LucaEstiva/Hobby_8088_PC/CPLD/Immagini/Altera_Quartus_BUS_Controller.png

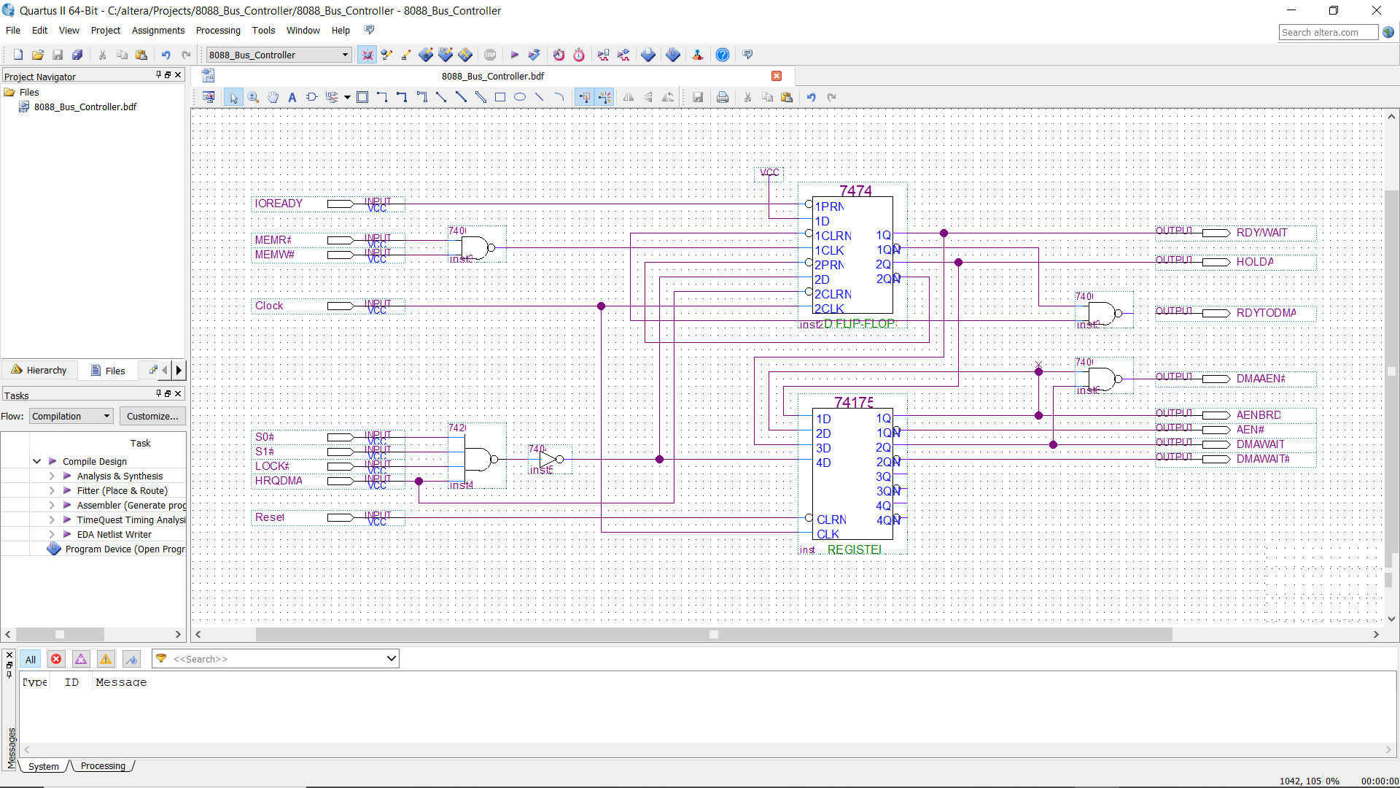
CPLD/Immagini/Altera_Quartus_BUS_Controller.png
