LucaEstiva/Hobby_8088_PC/CPLD/Immagini/USB_Blaster_Descrizione_Segnali.jpg

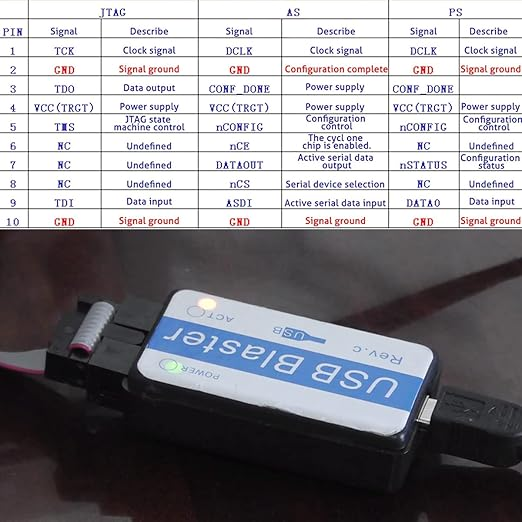
CPLD/Immagini/USB_Blaster_Descrizione_Segnali.jpg
