LucaEstiva/Hobby_8088_PC/Diagrammi/8088_Address_Data_Bus.png

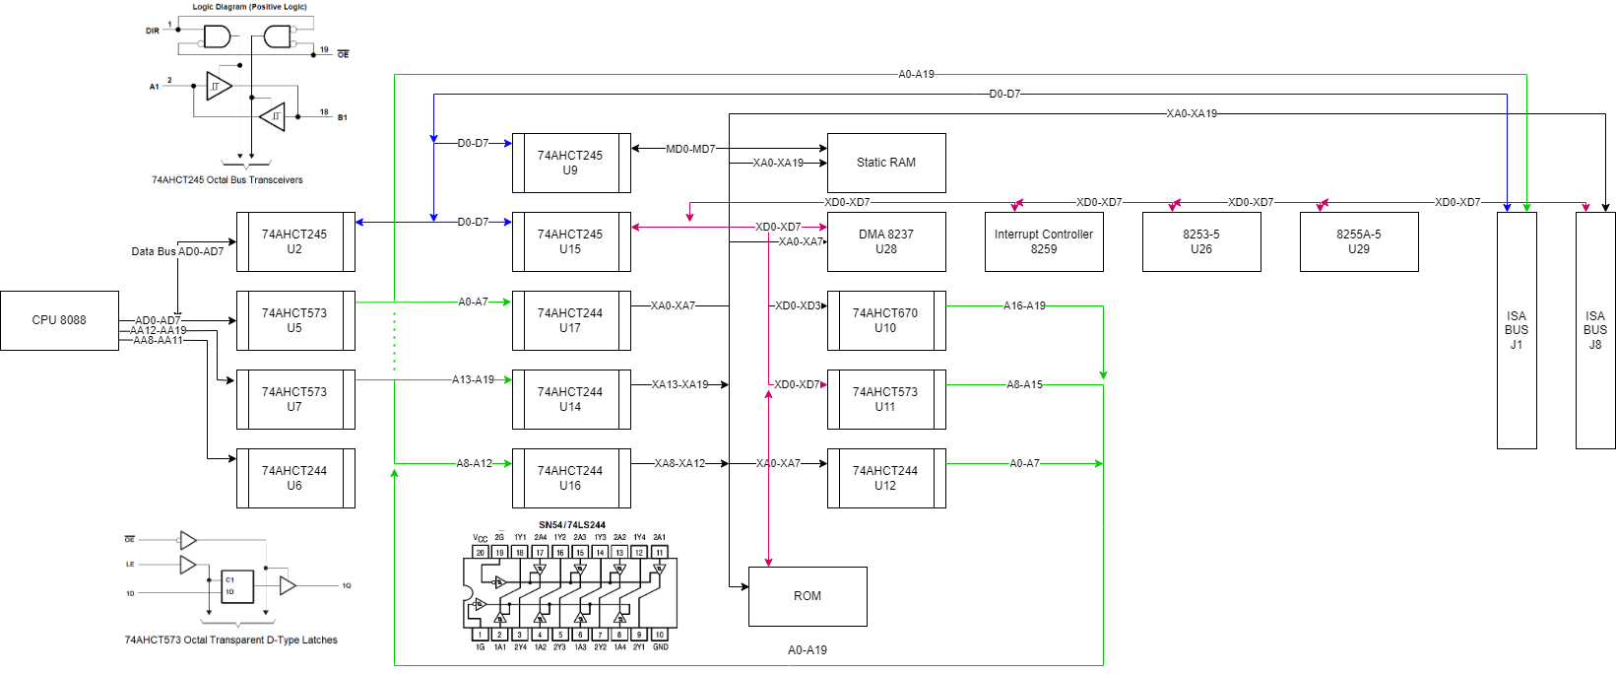
Diagrammi/8088_Address_Data_Bus.png
