LucaEstiva/Hobby_8088_PC/Diagrammi/AT29C010A.png

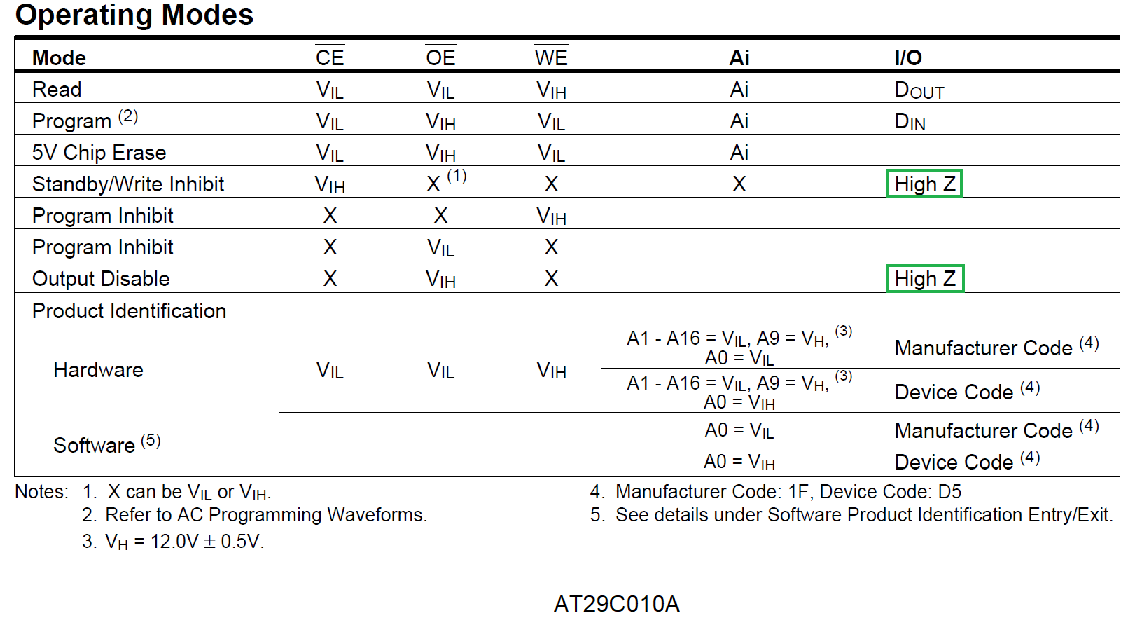
Diagrammi/AT29C010A.png
