LucaEstiva/Hobby_8088_PC/Diagrammi/HM628512C.png

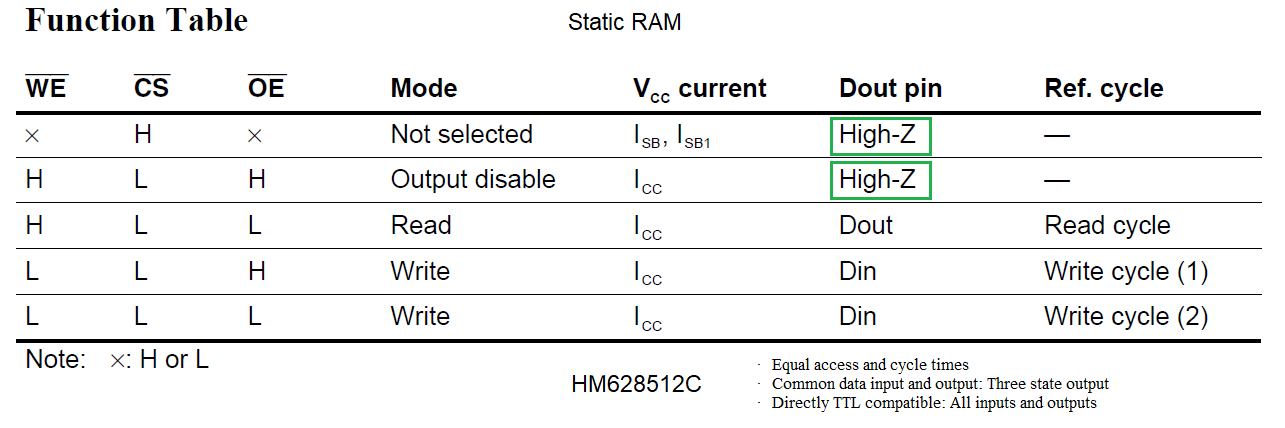
Diagrammi/HM628512C.png
