LucaEstiva/Hobby_8088_PC/FlipFlop/D_Flip-Flop_Async_PRE_CLEAR.png

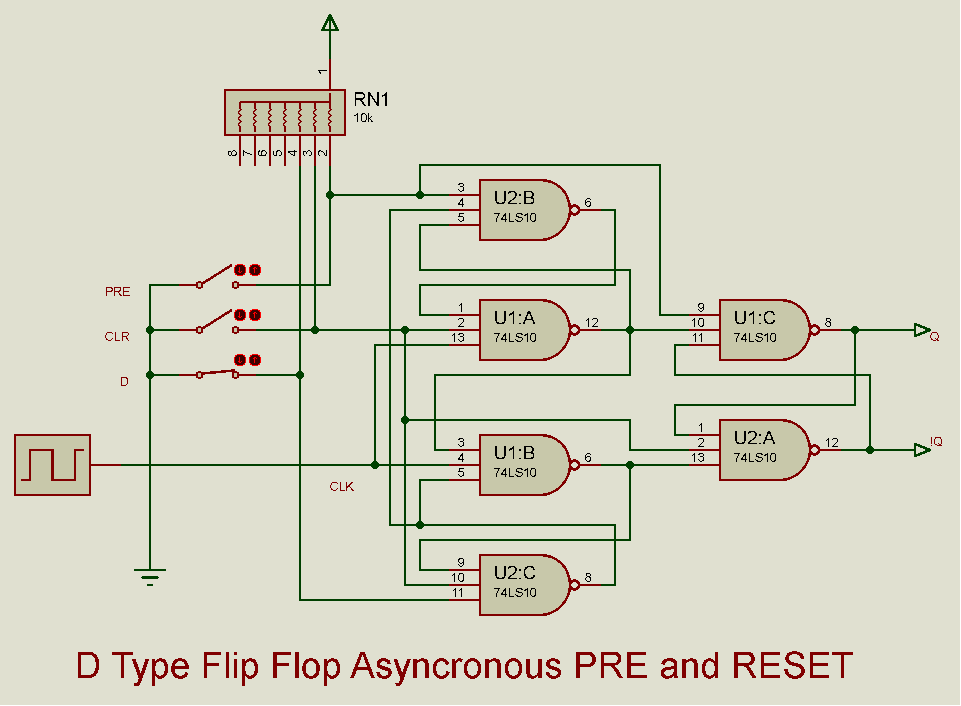
FlipFlop/D_Flip-Flop_Async_PRE_CLEAR.png
