LucaEstiva/Hobby_8088_PC/FlipFlop/D_Pre_Clear.png

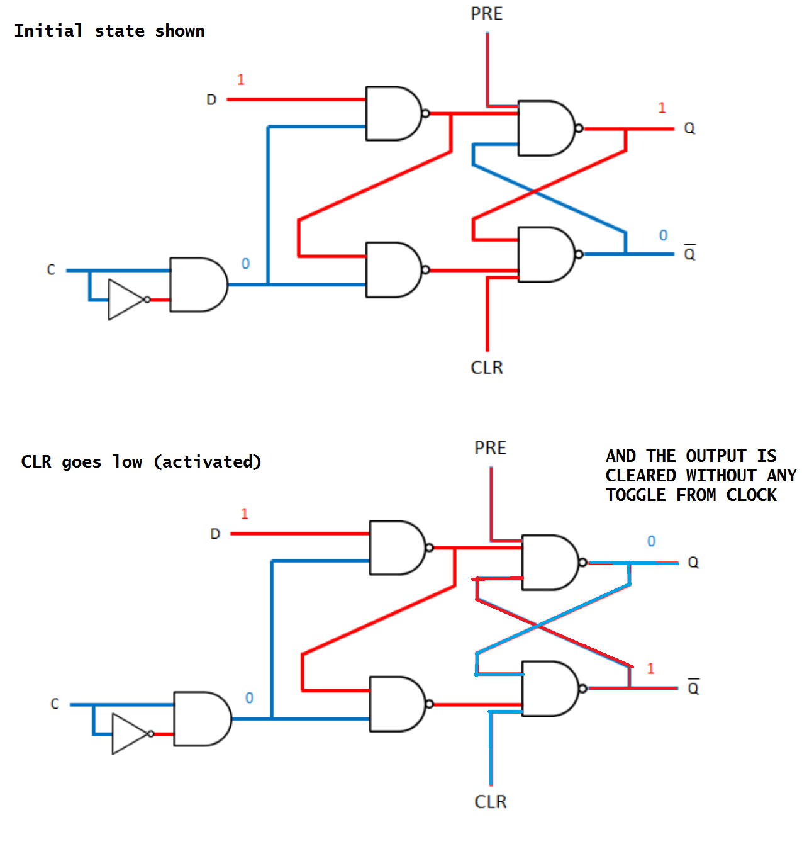
FlipFlop/D_Pre_Clear.png
