LucaEstiva/Hobby_8088_PC/GAL/Async_PRE_CLR.png

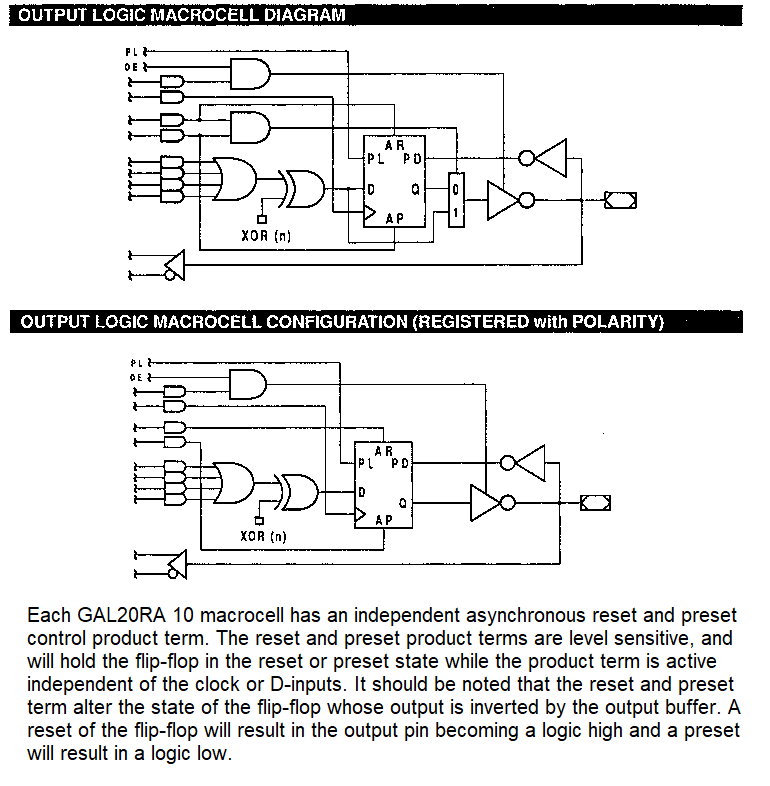
GAL/Async_PRE_CLR.png
