LucaEstiva/Hobby_8088_PC/GAL/Bus_Logic.png

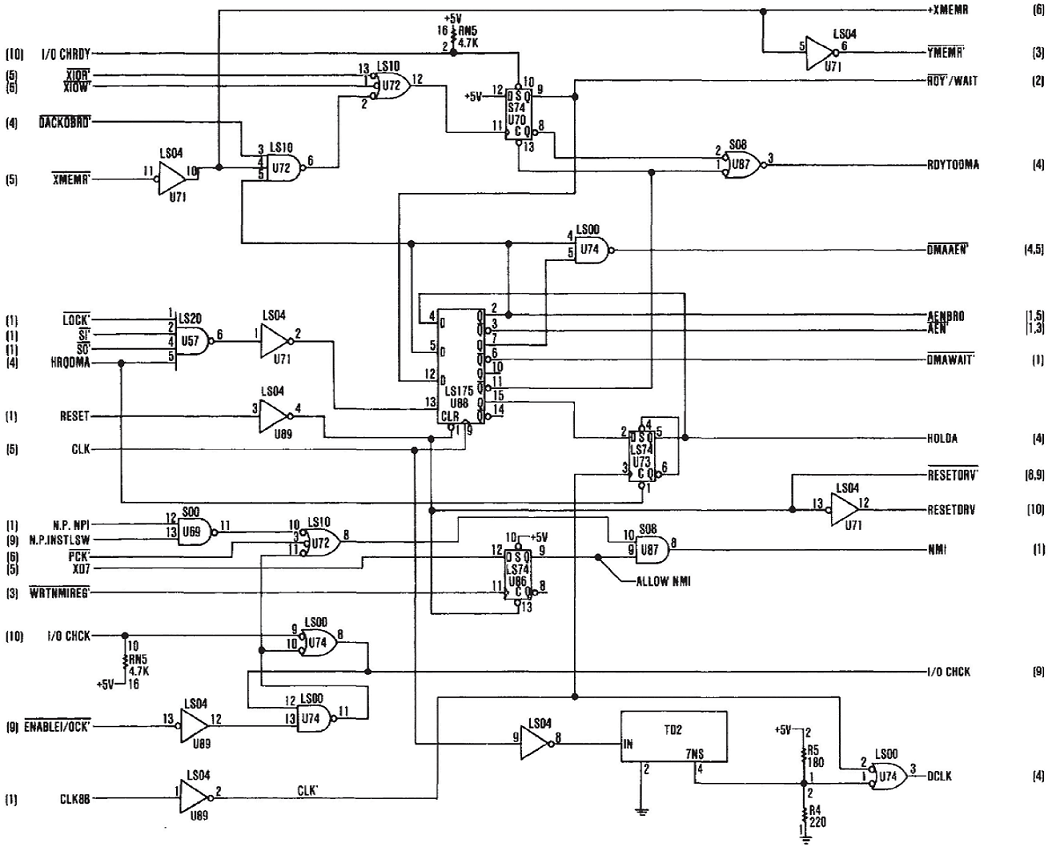
GAL/Bus_Logic.png
