LucaEstiva/Hobby_8088_PC/GAL/Bus_Logic_1.png

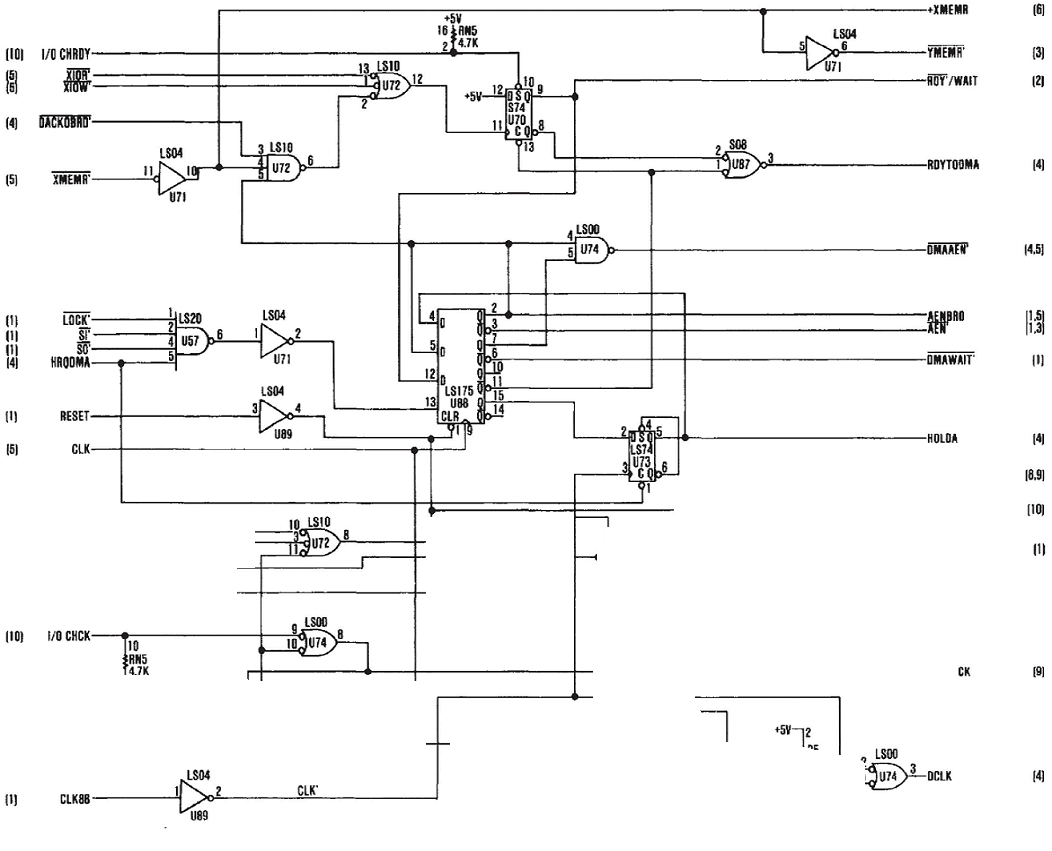
GAL/Bus_Logic_1.png
