LucaEstiva/Hobby_8088_PC/GAL/Bus_Logic_2.png

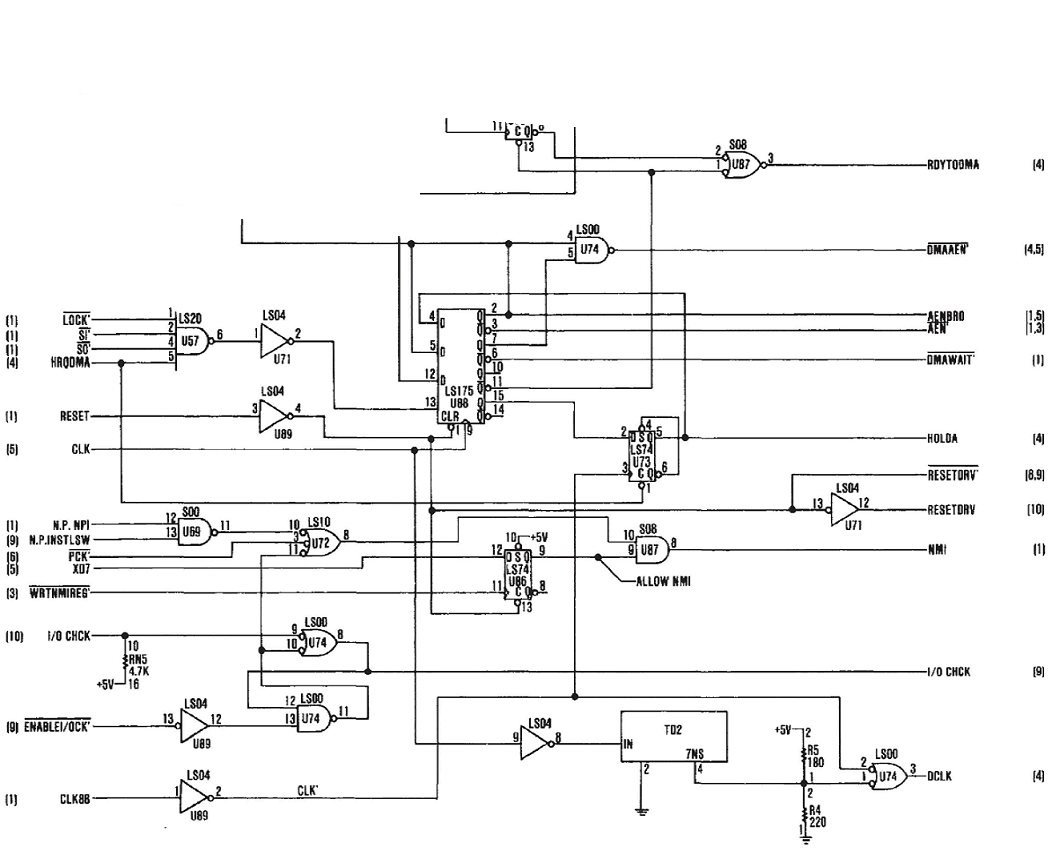
GAL/Bus_Logic_2.png
