LucaEstiva/Hobby_8088_PC/GAL/Bus_Logic_3.png

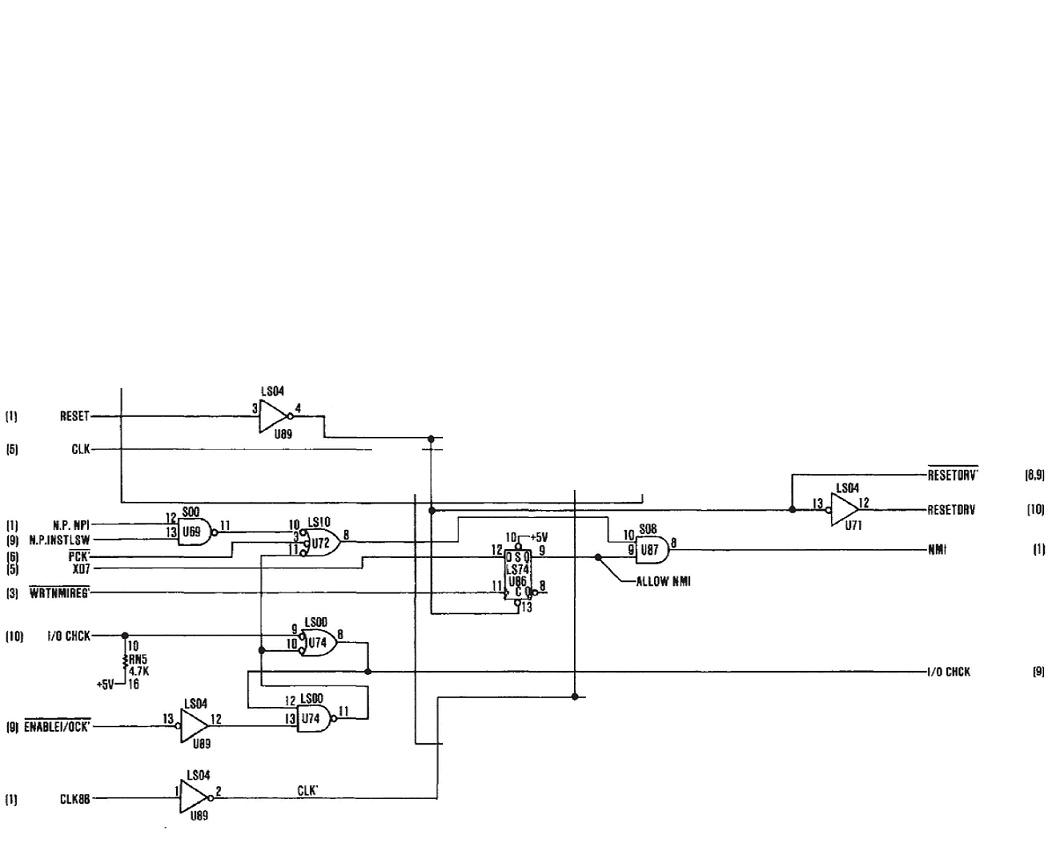
GAL/Bus_Logic_3.png
