LucaEstiva/Hobby_8088_PC/GAL/Bus_Logic_4.png

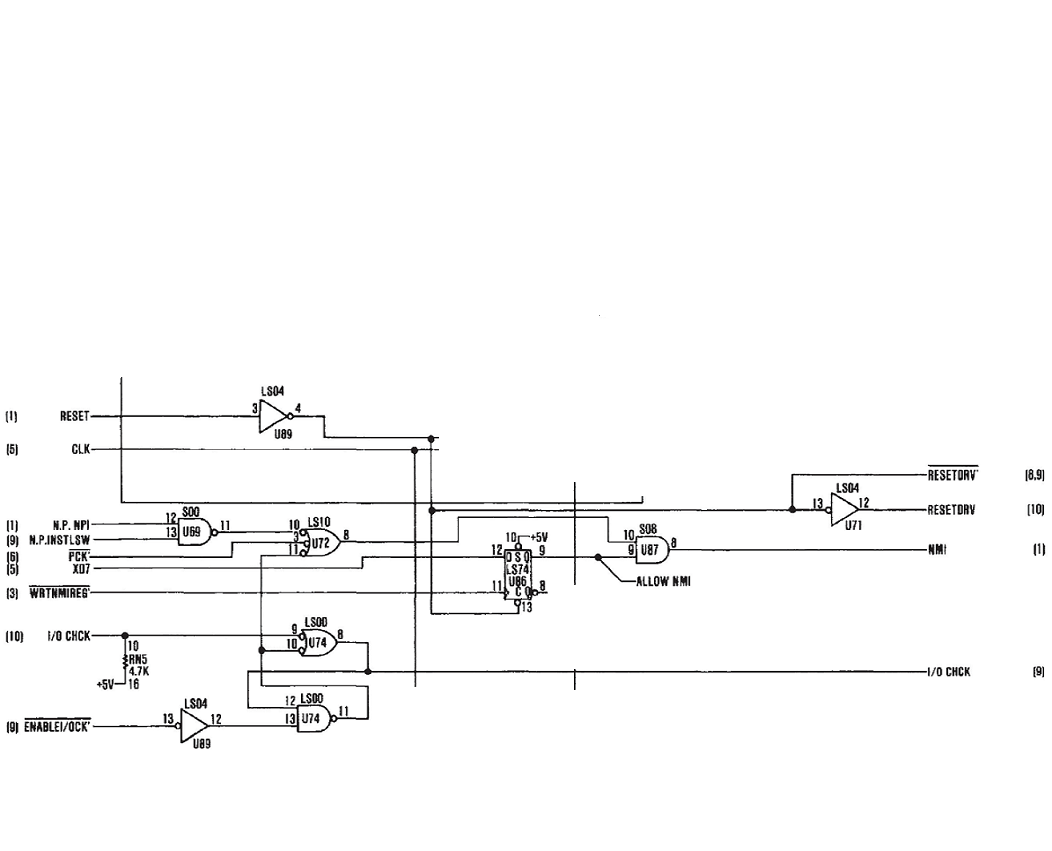
GAL/Bus_Logic_4.png
