LucaEstiva/Hobby_8088_PC/GAL/Bus_Logic_5.png

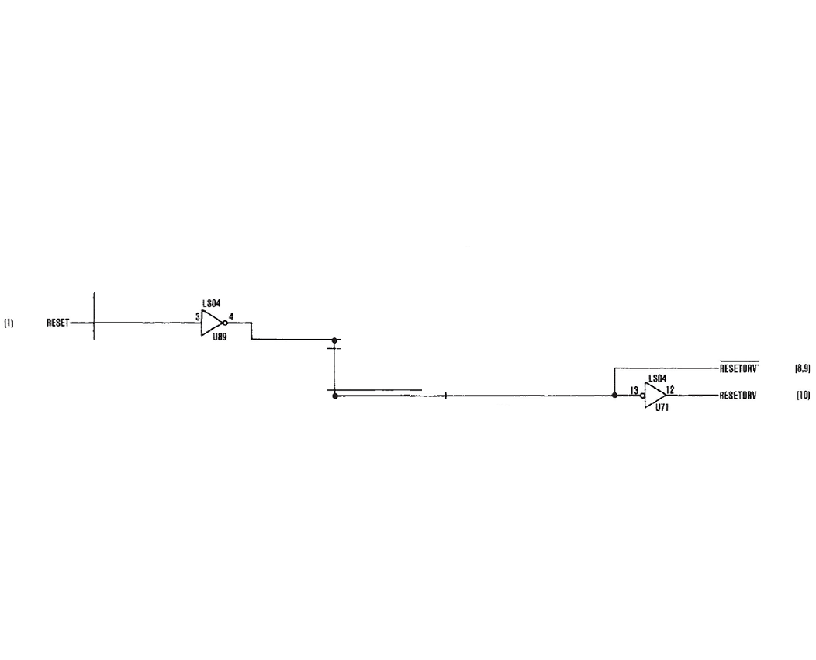
GAL/Bus_Logic_5.png
