LucaEstiva/Hobby_8088_PC/GAL/Bus_Logic_6.png

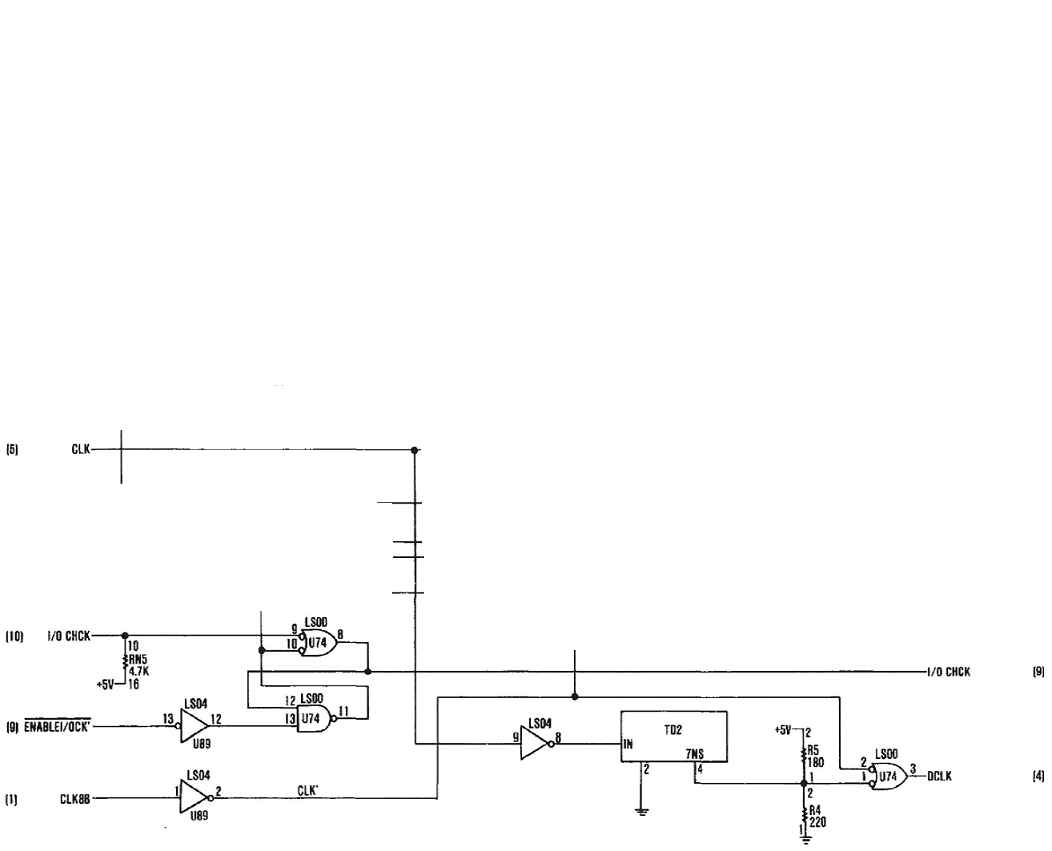
GAL/Bus_Logic_6.png
