LucaEstiva/Hobby_8088_PC/GAL/Bus_Logic_7.png

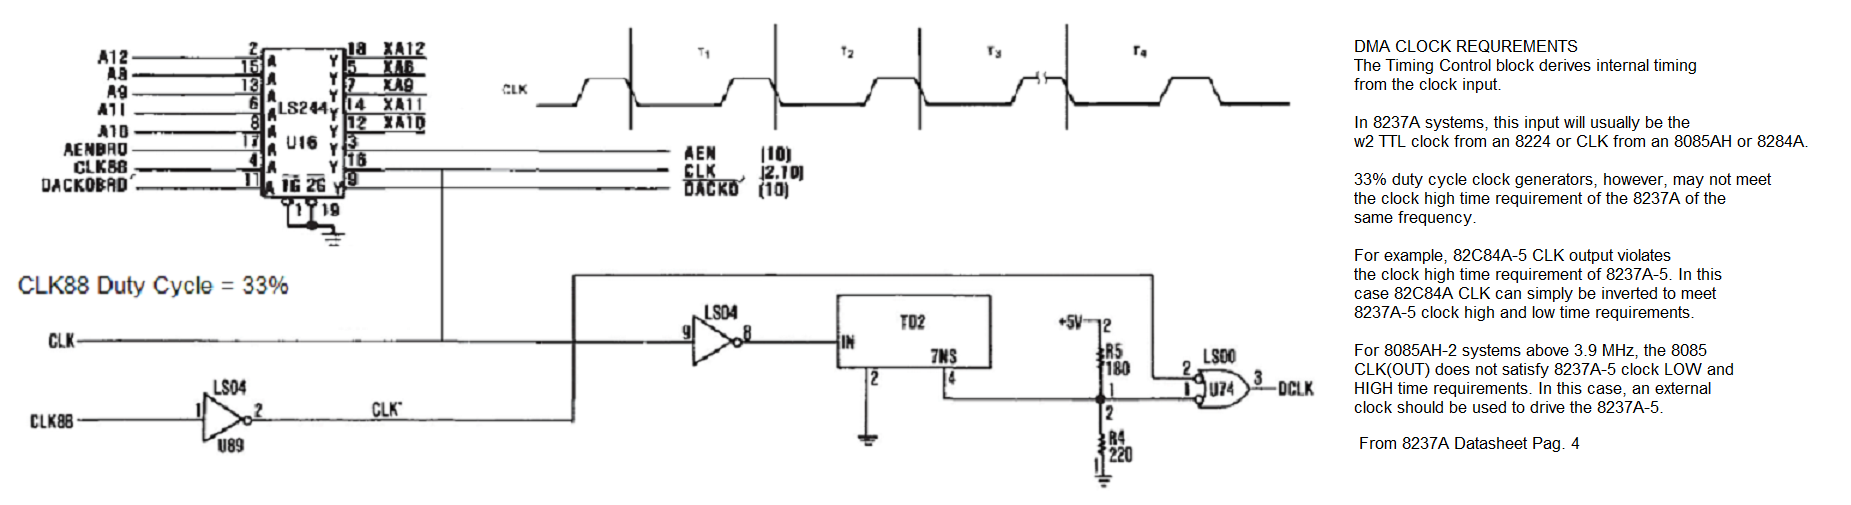
GAL/Bus_Logic_7.png
