LucaEstiva/Hobby_8088_PC/Logica/Bus_Part_1.png

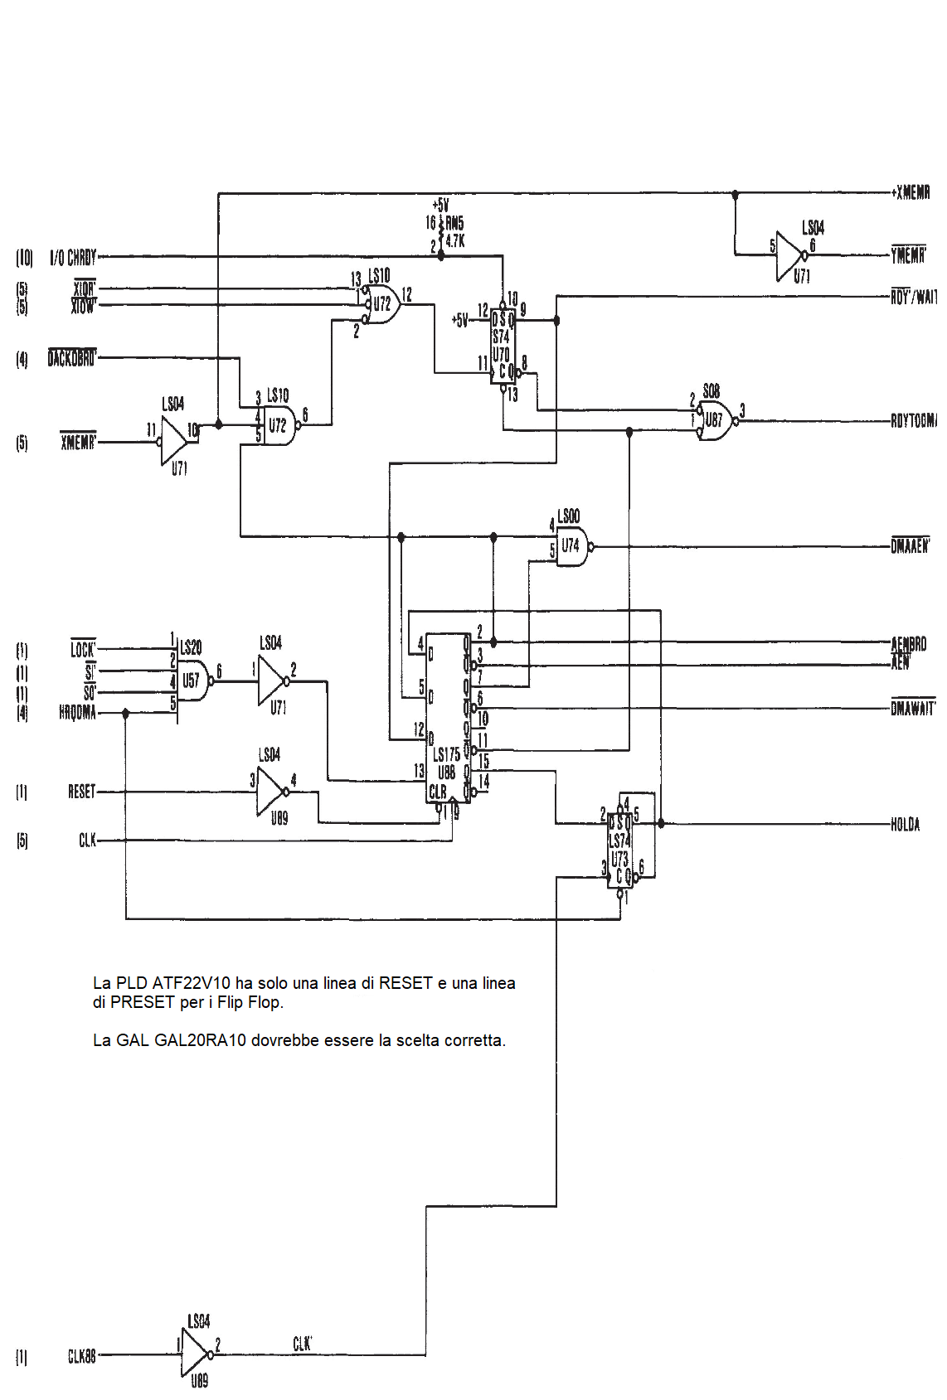
Logica/Bus_Part_1.png
