LucaEstiva/Hobby_8088_PC/Logica/Logic_Gates.png

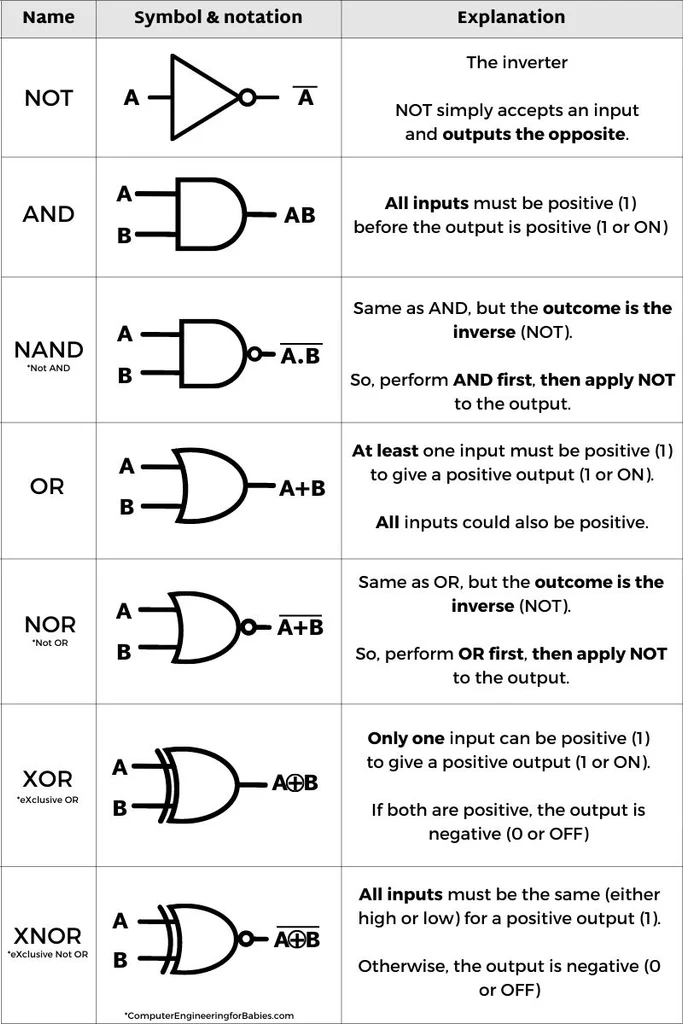
Logica/Logic_Gates.png
