LucaEstiva/Hobby_8088_PC/Simplyfied_Diagram/5150_5160_clock_generation.jpg

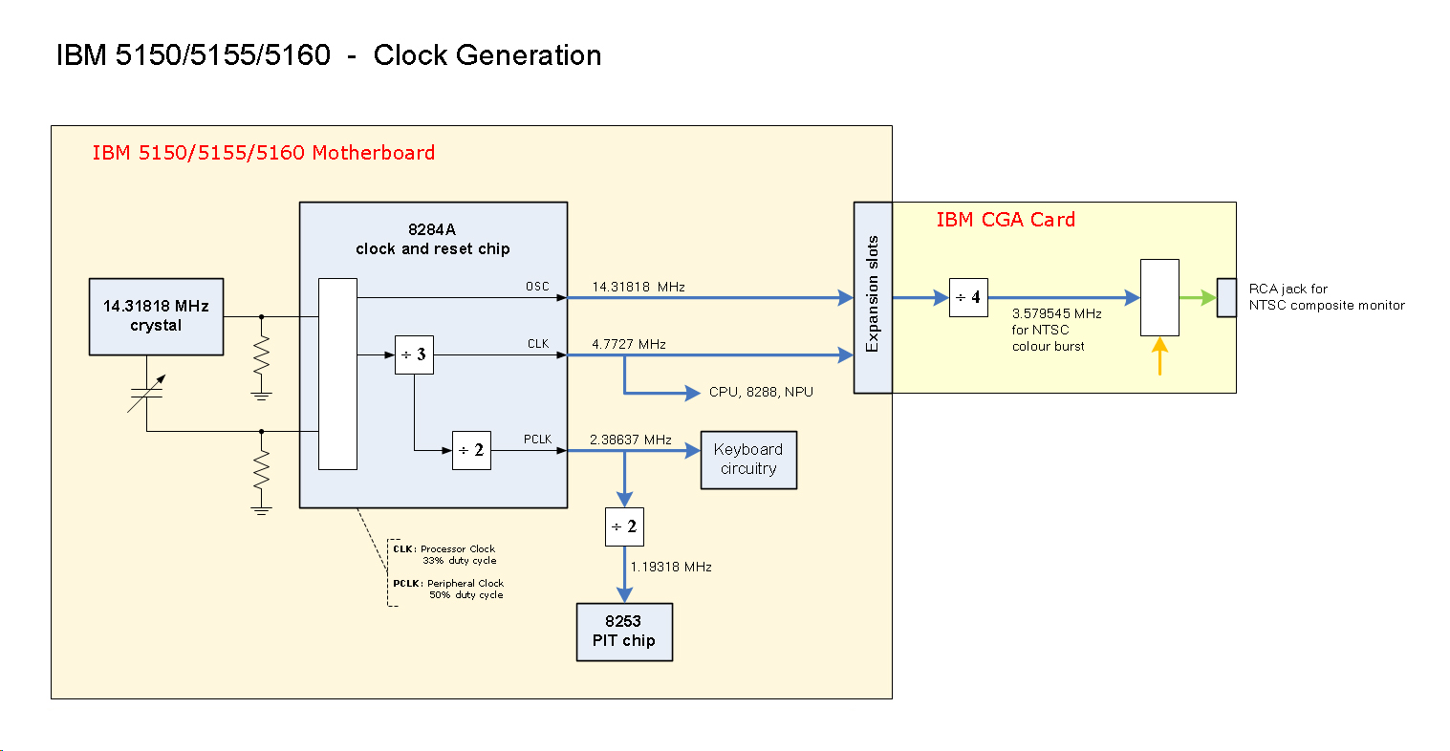
Simplyfied_Diagram/5150_5160_clock_generation.jpg
