LucaEstiva/Hobby_8088_PC/Simplyfied_Diagram/5150_5160_motherboard_ram_layout.jpg

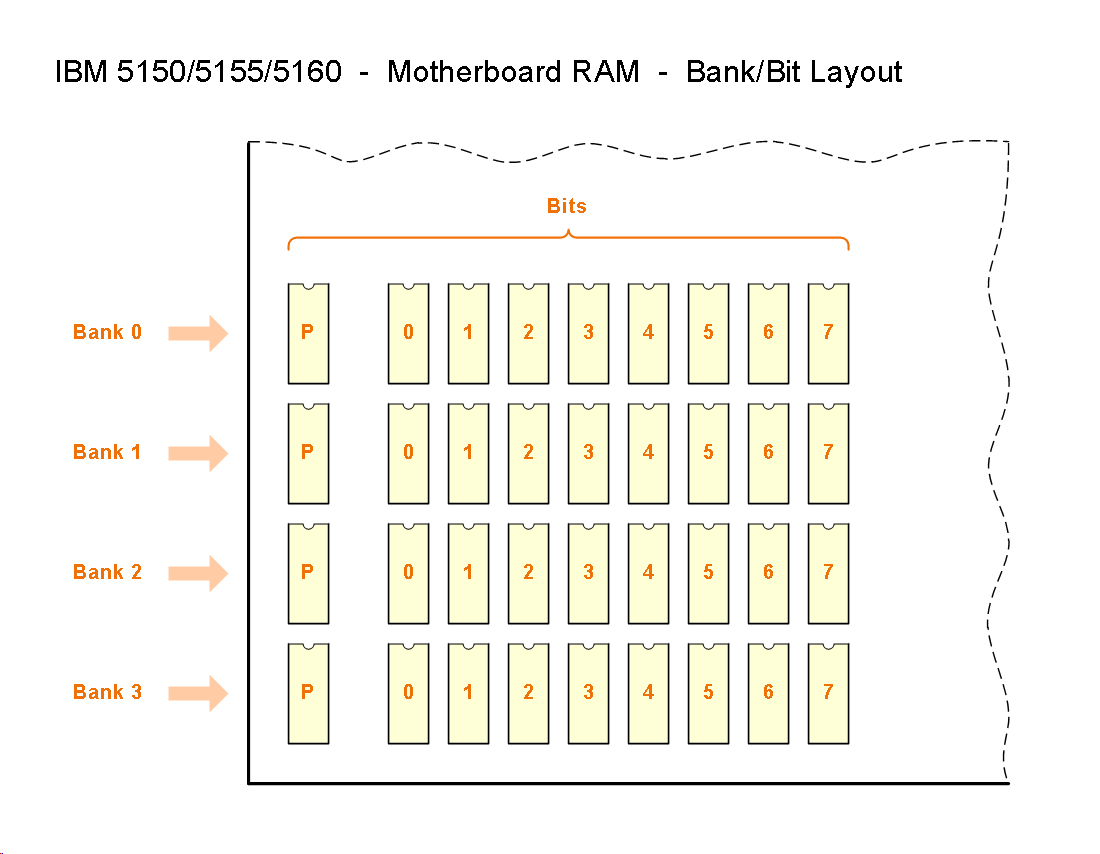
Simplyfied_Diagram/5150_5160_motherboard_ram_layout.jpg
