LucaEstiva/Hobby_8088_PC/Simplyfied_Diagram/5160_address_bus.jpg

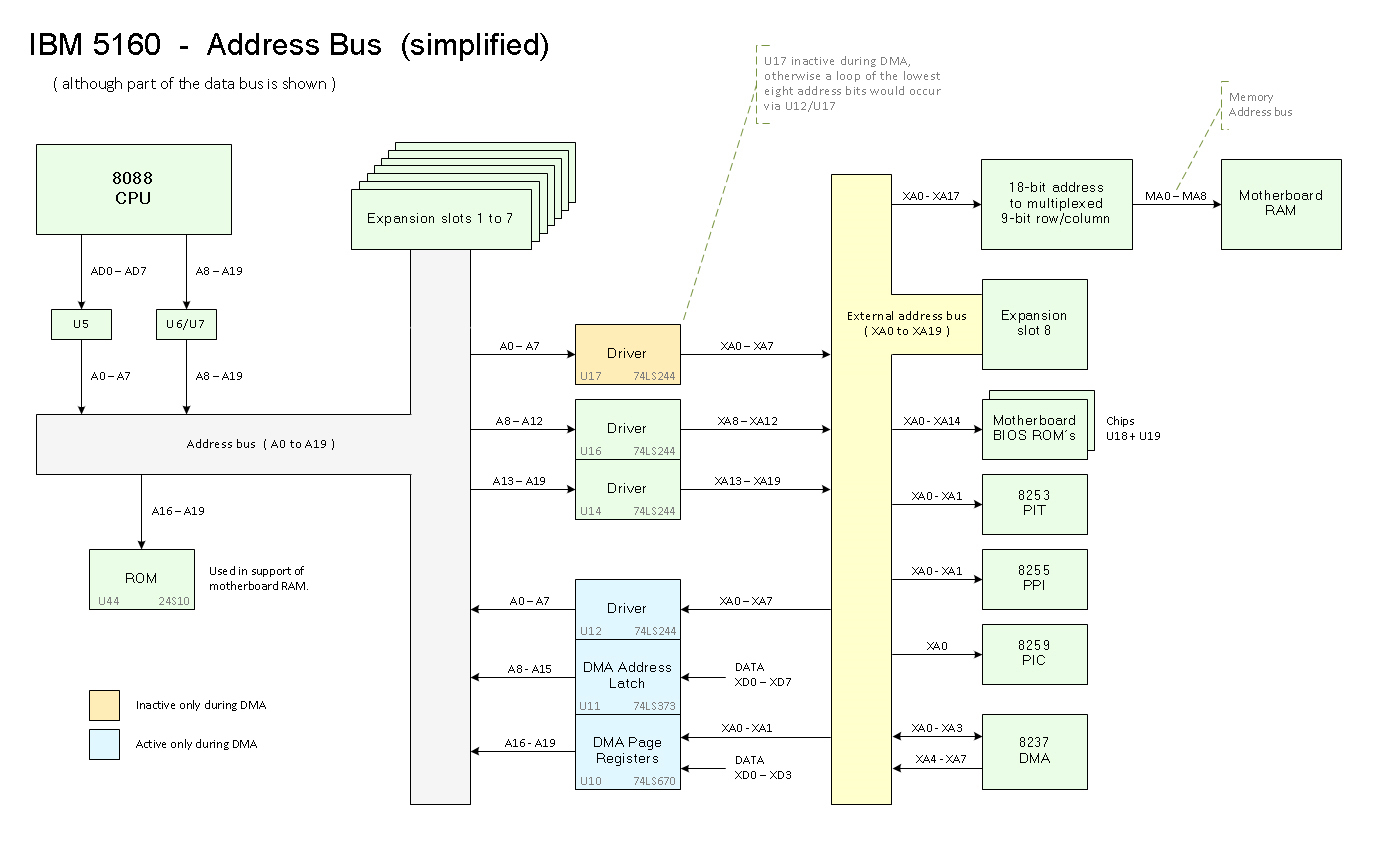
Simplyfied_Diagram/5160_address_bus.jpg
