LucaEstiva/Hobby_8088_PC/Simplyfied_Diagram/5160_data_bus.jpg

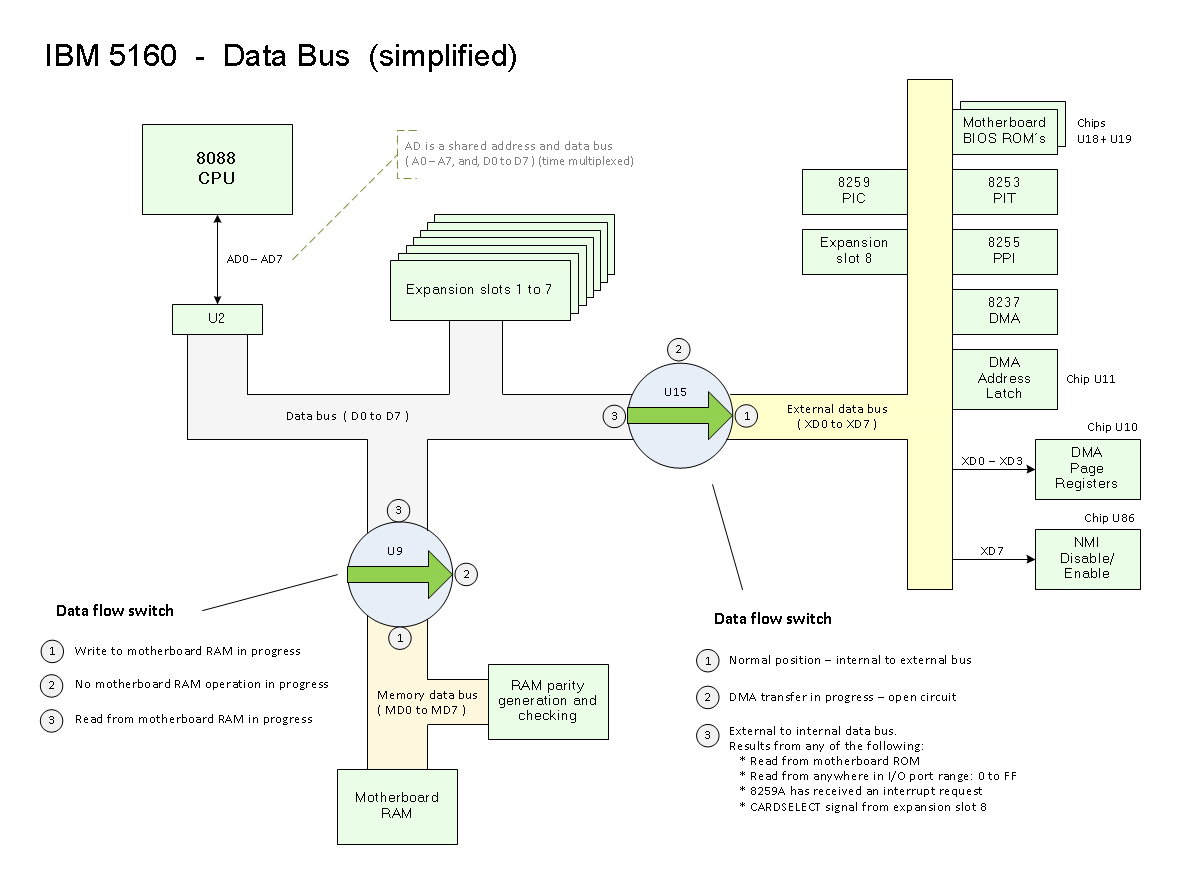
Simplyfied_Diagram/5160_data_bus.jpg
