LucaEstiva/Hobby_8088_PC/Simplyfied_Diagram/5160_digital_output_via_8255_PB2.jpg

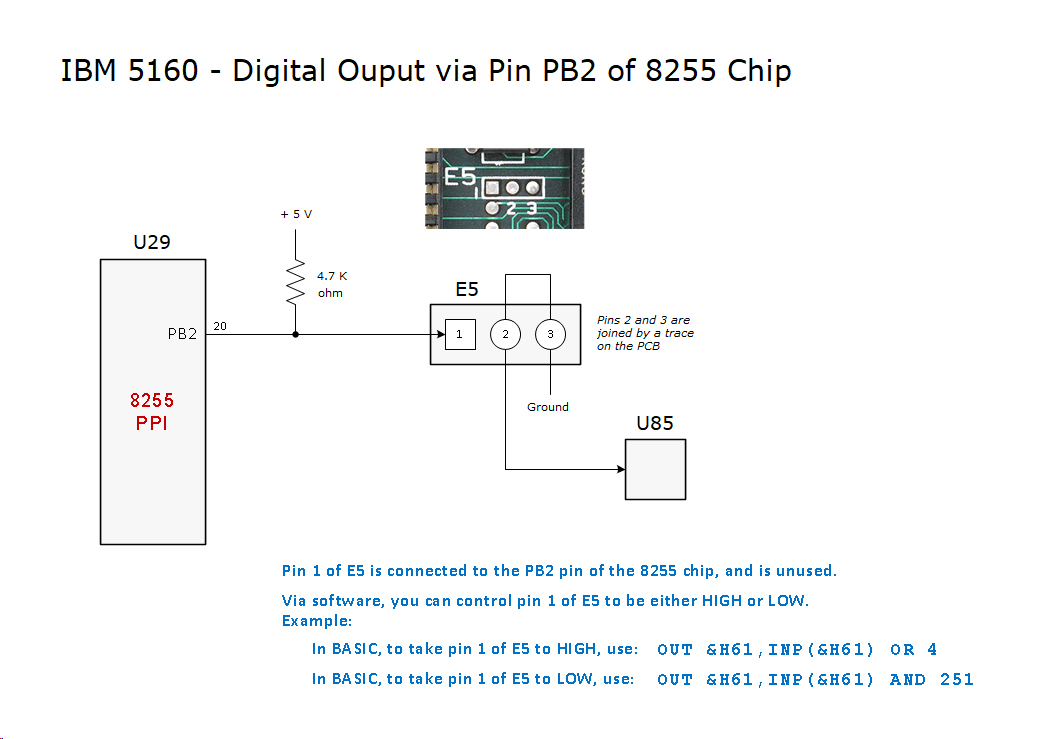
Simplyfied_Diagram/5160_digital_output_via_8255_PB2.jpg
