LucaEstiva/Hobby_8088_PC/Simplyfied_Diagram/5160_memory_layout_of_bios_and_basic.jpg

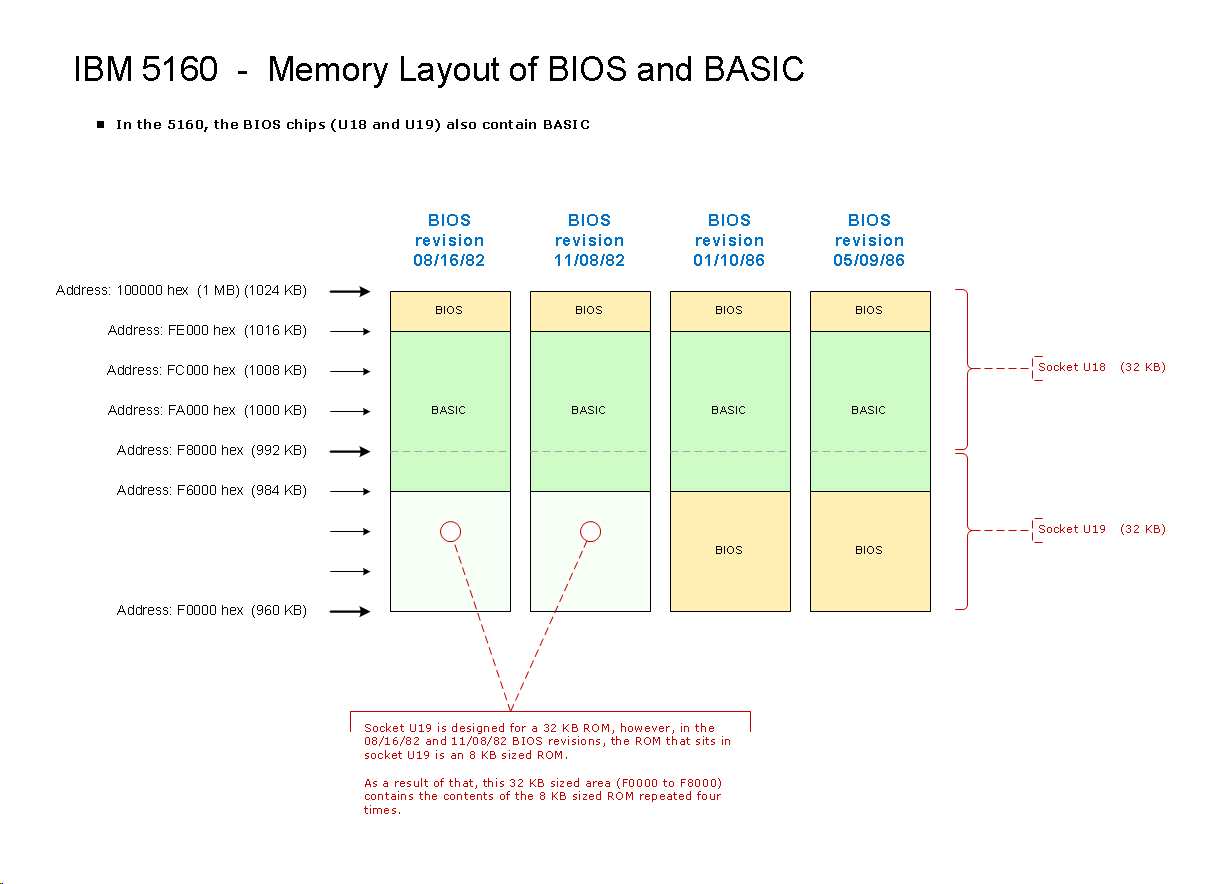
Simplyfied_Diagram/5160_memory_layout_of_bios_and_basic.jpg
