LucaEstiva/Hobby_8088_PC/Simplyfied_Diagram/5160_nmi_generation.jpg

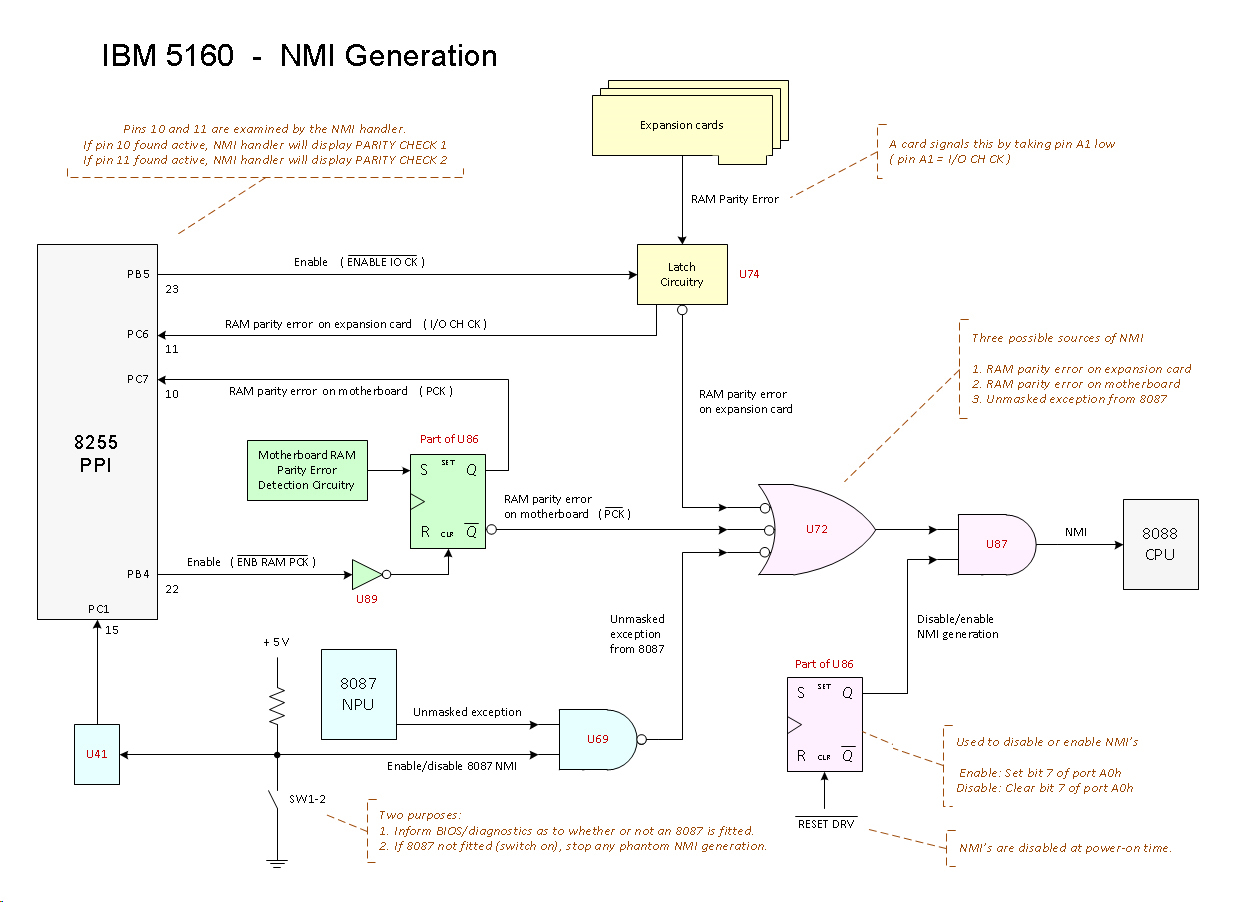
Simplyfied_Diagram/5160_nmi_generation.jpg
