LucaEstiva/Hobby_8088_PC/Simplyfied_Diagram/5160_speaker_circuit.jpg

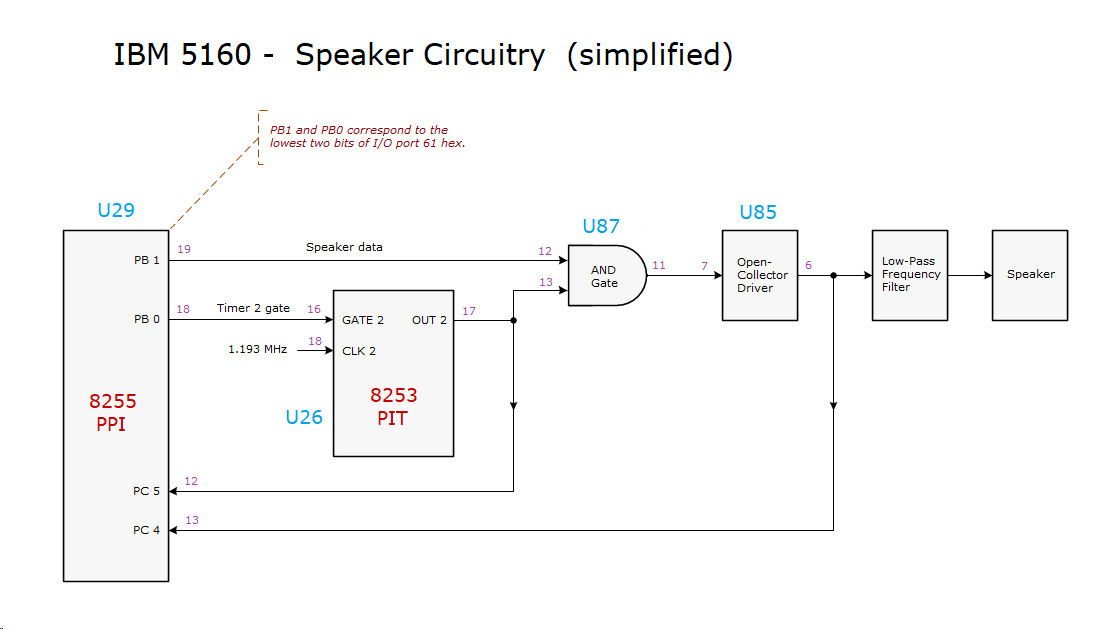
Simplyfied_Diagram/5160_speaker_circuit.jpg
