LucaEstiva/Hobby_8088_PC/Simplyfied_Diagram/IBM 5160 motherboard - 256-640KB - External address bus to memory address bus.png

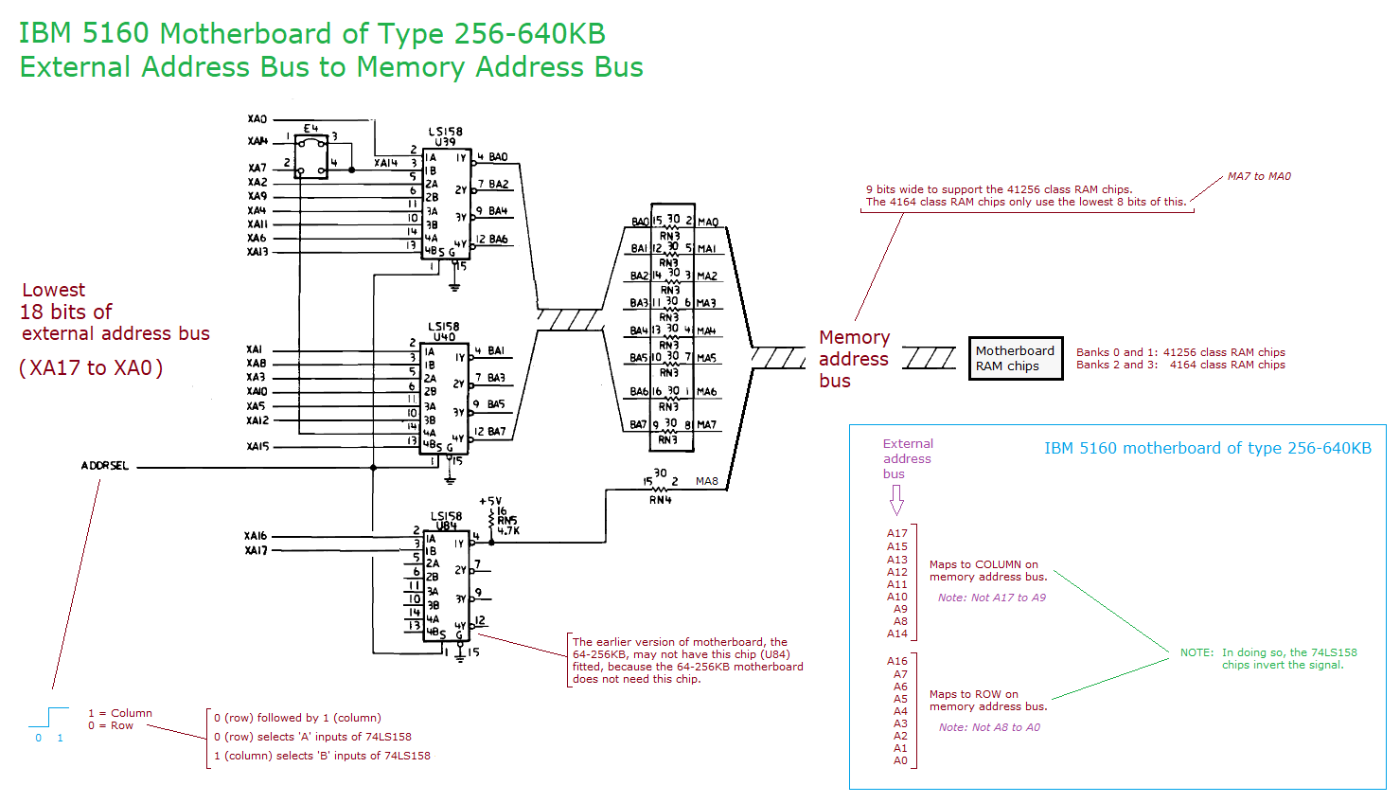
Simplyfied_Diagram/IBM 5160 motherboard - 256-640KB - External address bus to memory address bus.png
