LucaEstiva/Hobby_8088_PC/Simplyfied_Diagram/IBM 5160 motherboard - 8088 CPU to address bus.png

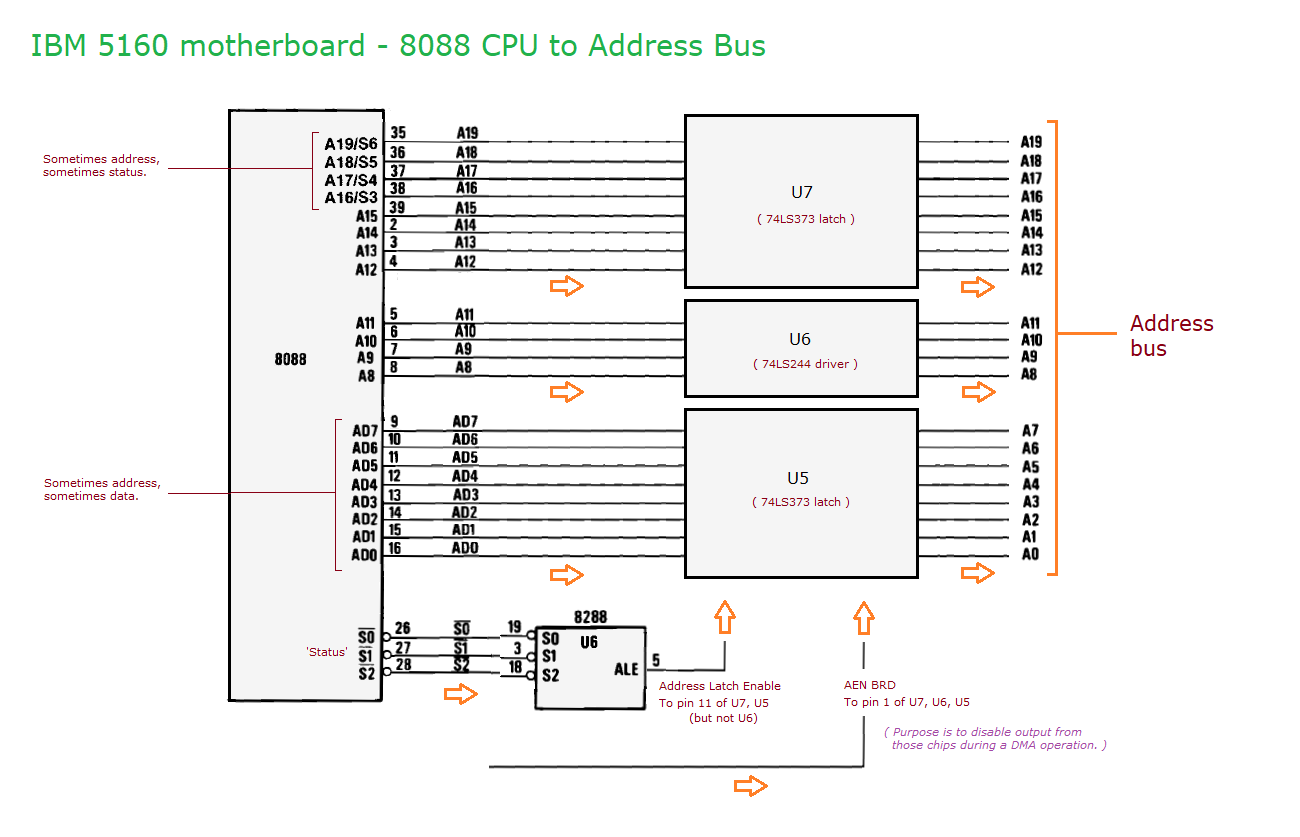
Simplyfied_Diagram/IBM 5160 motherboard - 8088 CPU to address bus.png
