LucaEstiva/Hobby_8088_PC/Simplyfied_Diagram/IBM 5160 motherboard - 8253 circuitry.png

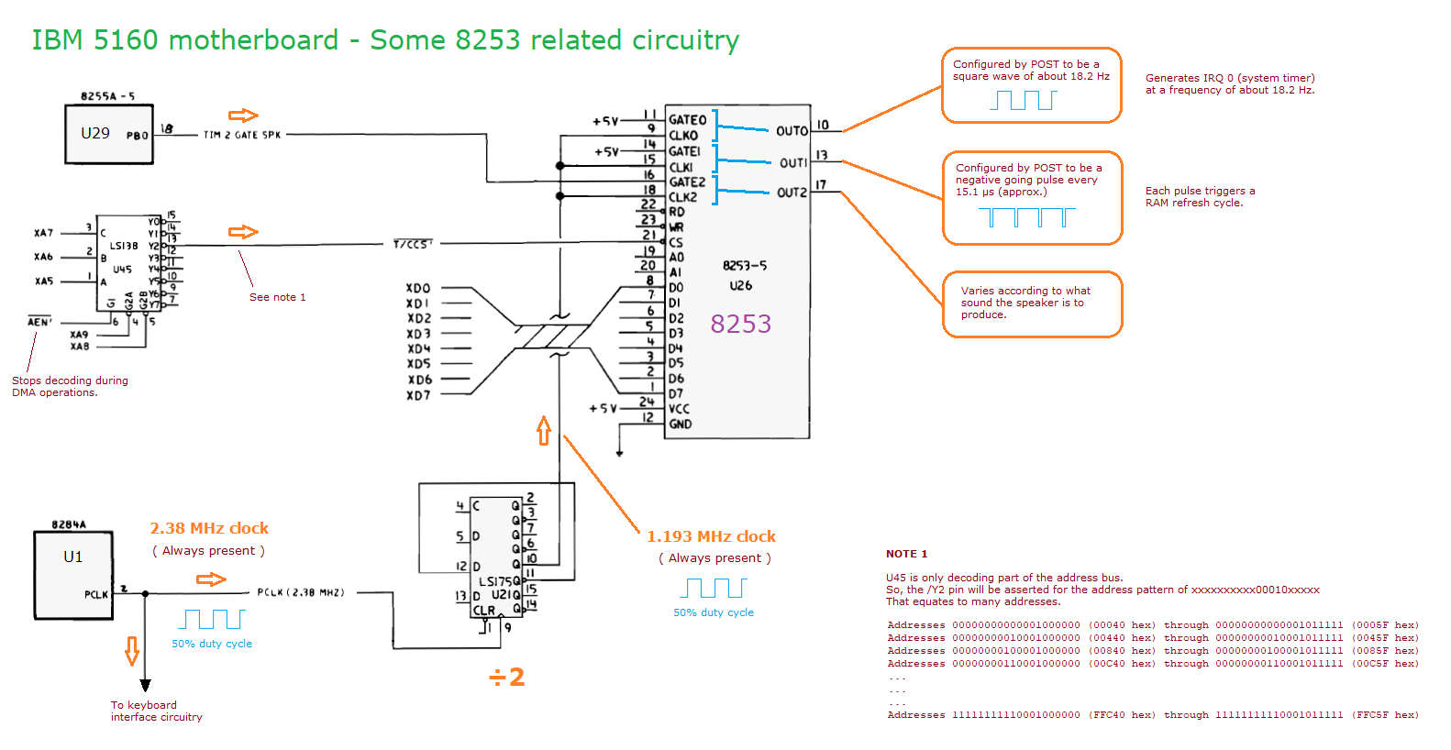
Simplyfied_Diagram/IBM 5160 motherboard - 8253 circuitry.png
