LucaEstiva/Hobby_8088_PC/Simplyfied_Diagram/IBM 5160 motherboard - CAS and RAMADDRSEL generation.png

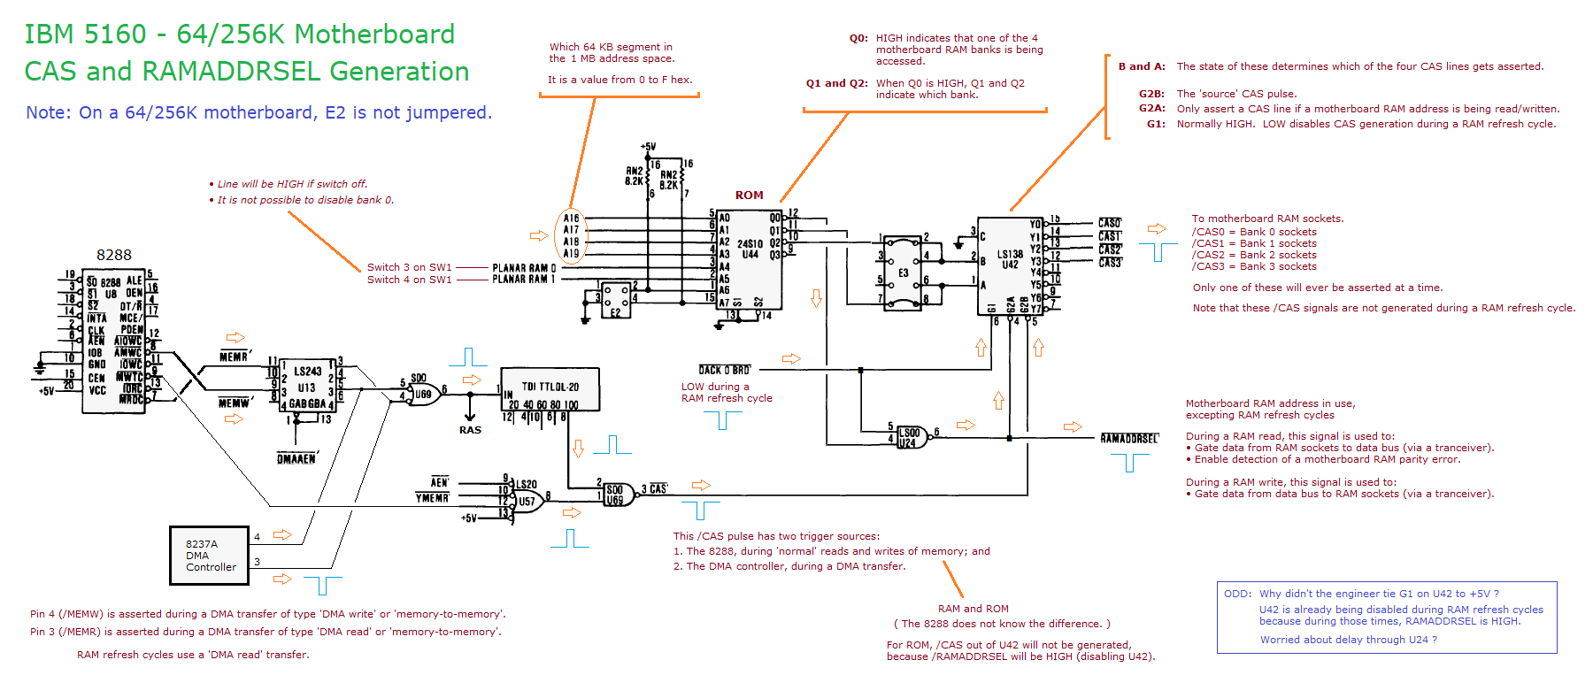
Simplyfied_Diagram/IBM 5160 motherboard - CAS and RAMADDRSEL generation.png
