LucaEstiva/Hobby_8088_PC/Simplyfied_Diagram/IBM 5160 motherboard - Generation of CS for U18 ROM.png

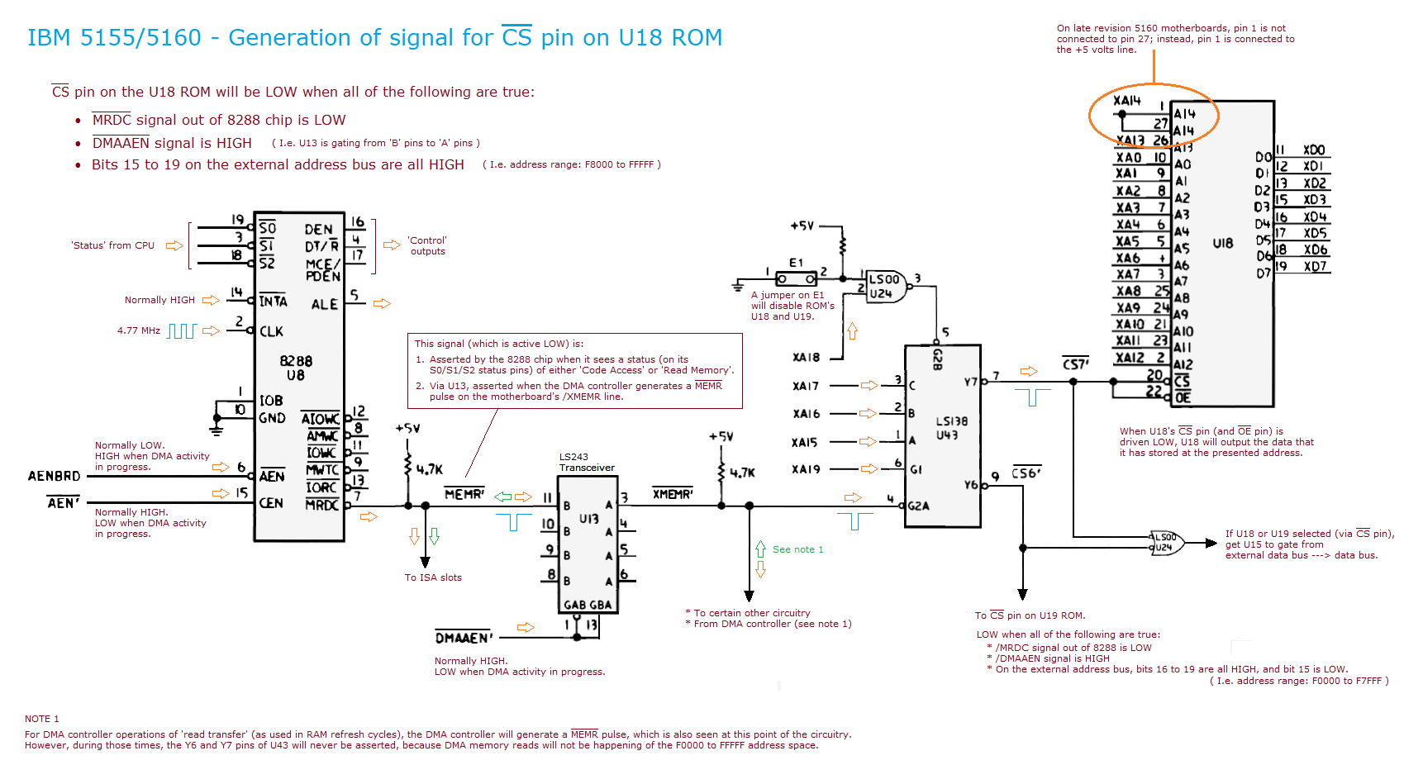
Simplyfied_Diagram/IBM 5160 motherboard - Generation of CS for U18 ROM.png
