LucaEstiva/Hobby_8088_PC/Simplyfied_Diagram/IBM 5160 motherboard - RAS CAS delay.png

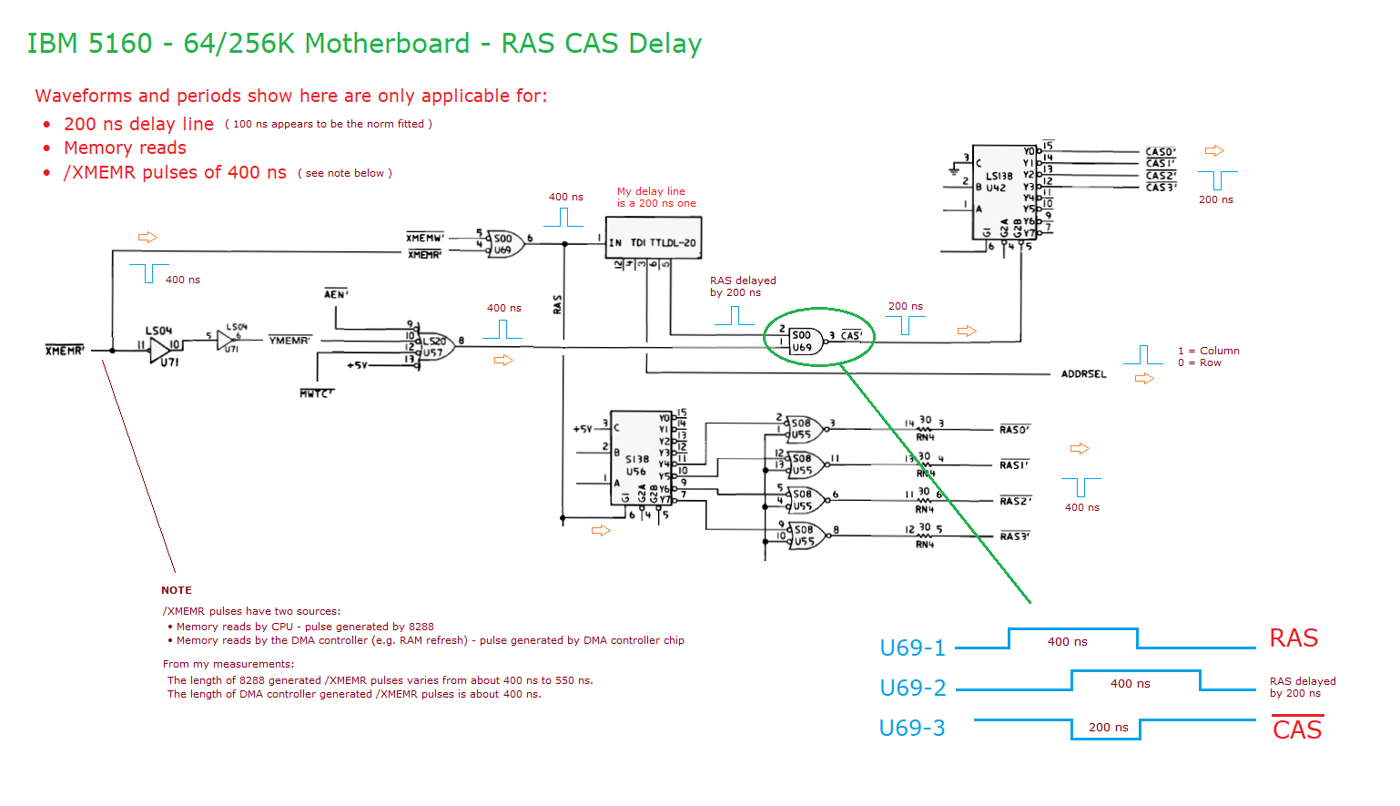
Simplyfied_Diagram/IBM 5160 motherboard - RAS CAS delay.png
