LucaEstiva/Hobby_8088_PC/Schemi/Revisioni/7/Logica_GLUE_Logic.pdf

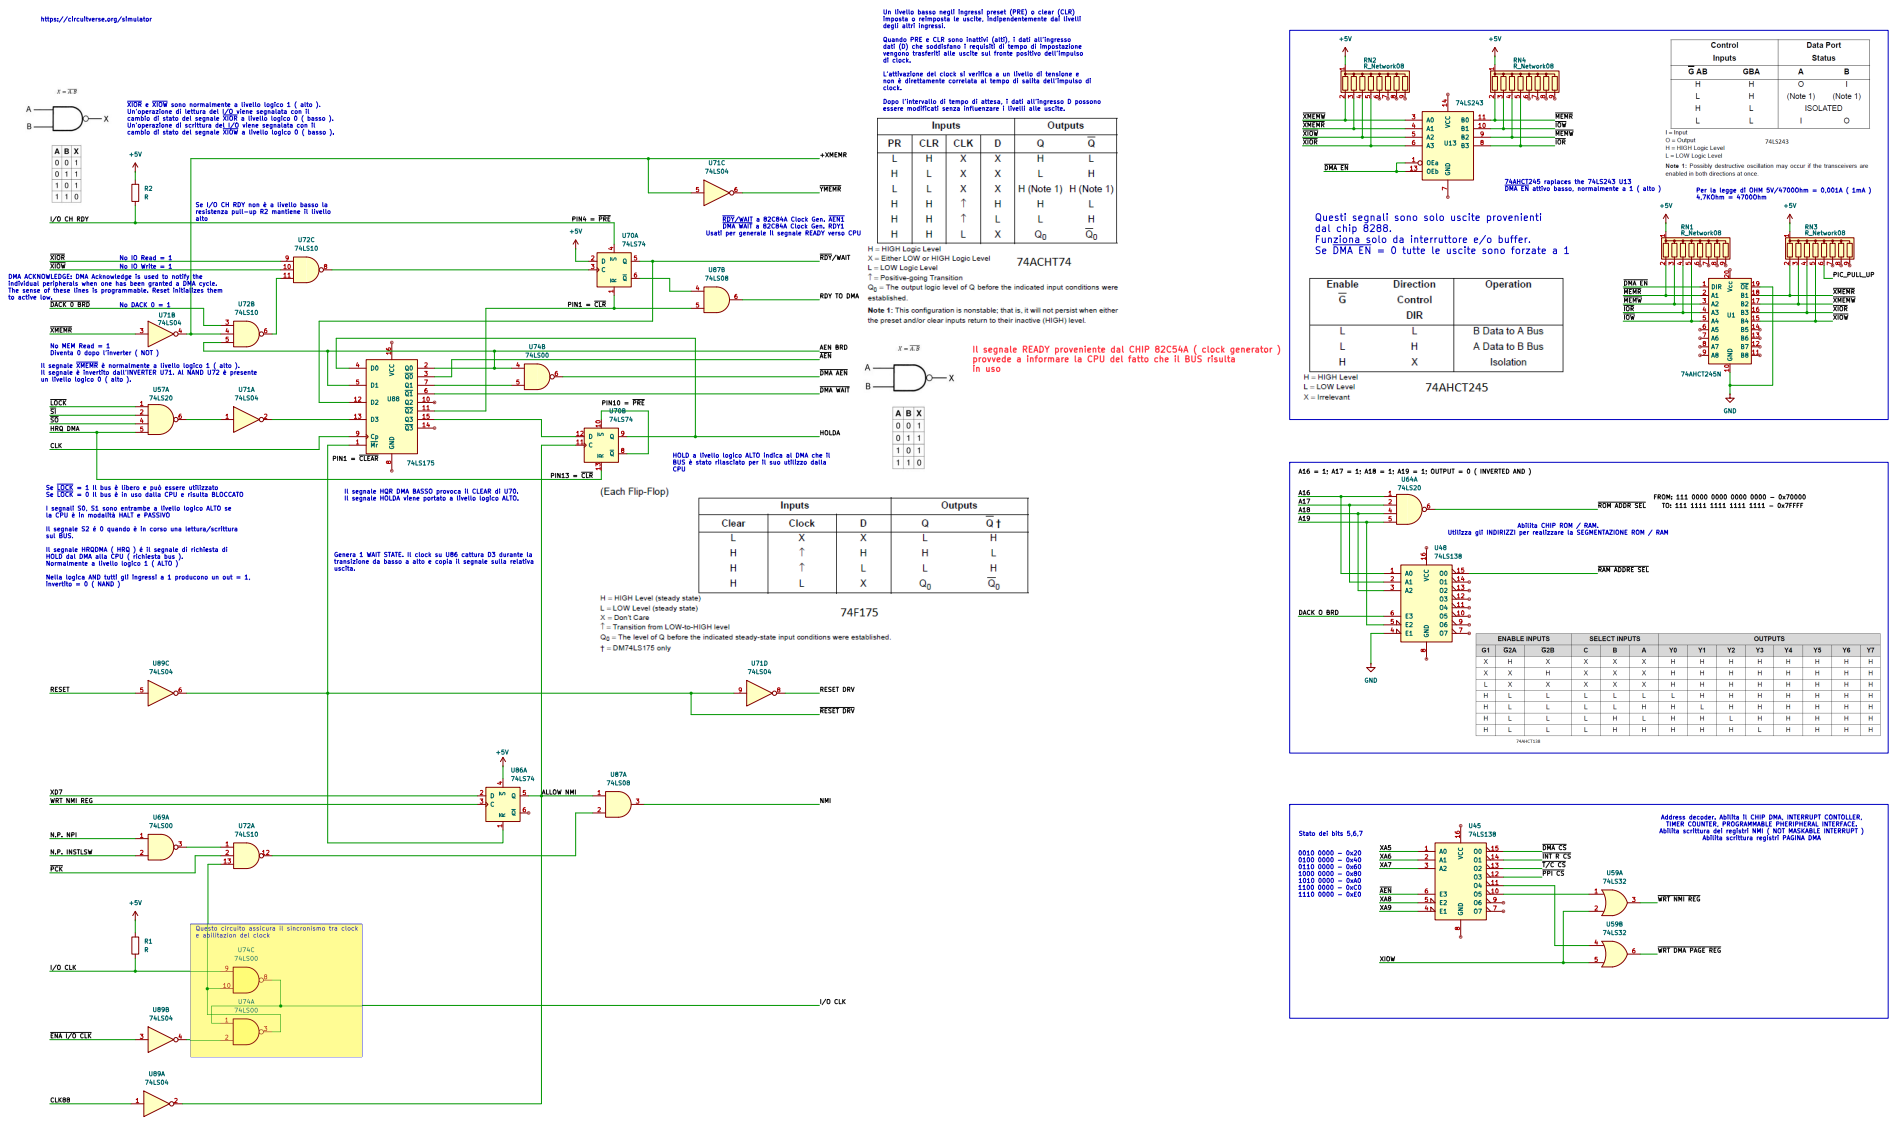
[picture p49: page 1]
