LucaEstiva/Hobby_8088_PC/Schemi/Revisioni/7/Principale.pdf

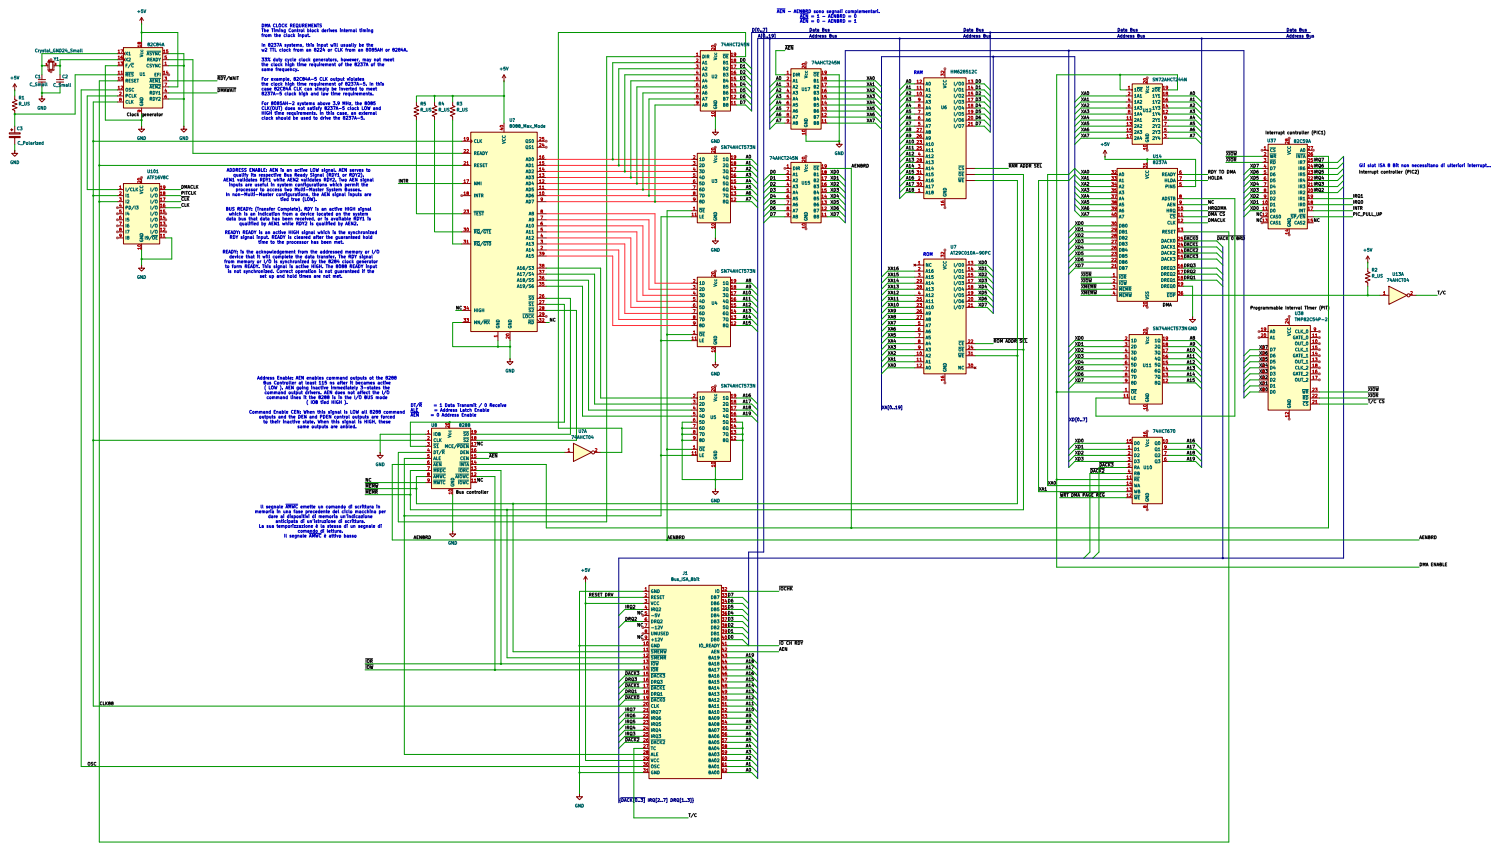
[picture p50: page 1]
