LucaEstiva/Hobby_8088_PC/Schemi/Revisioni/1/Principale_Correzzione_1.pdf

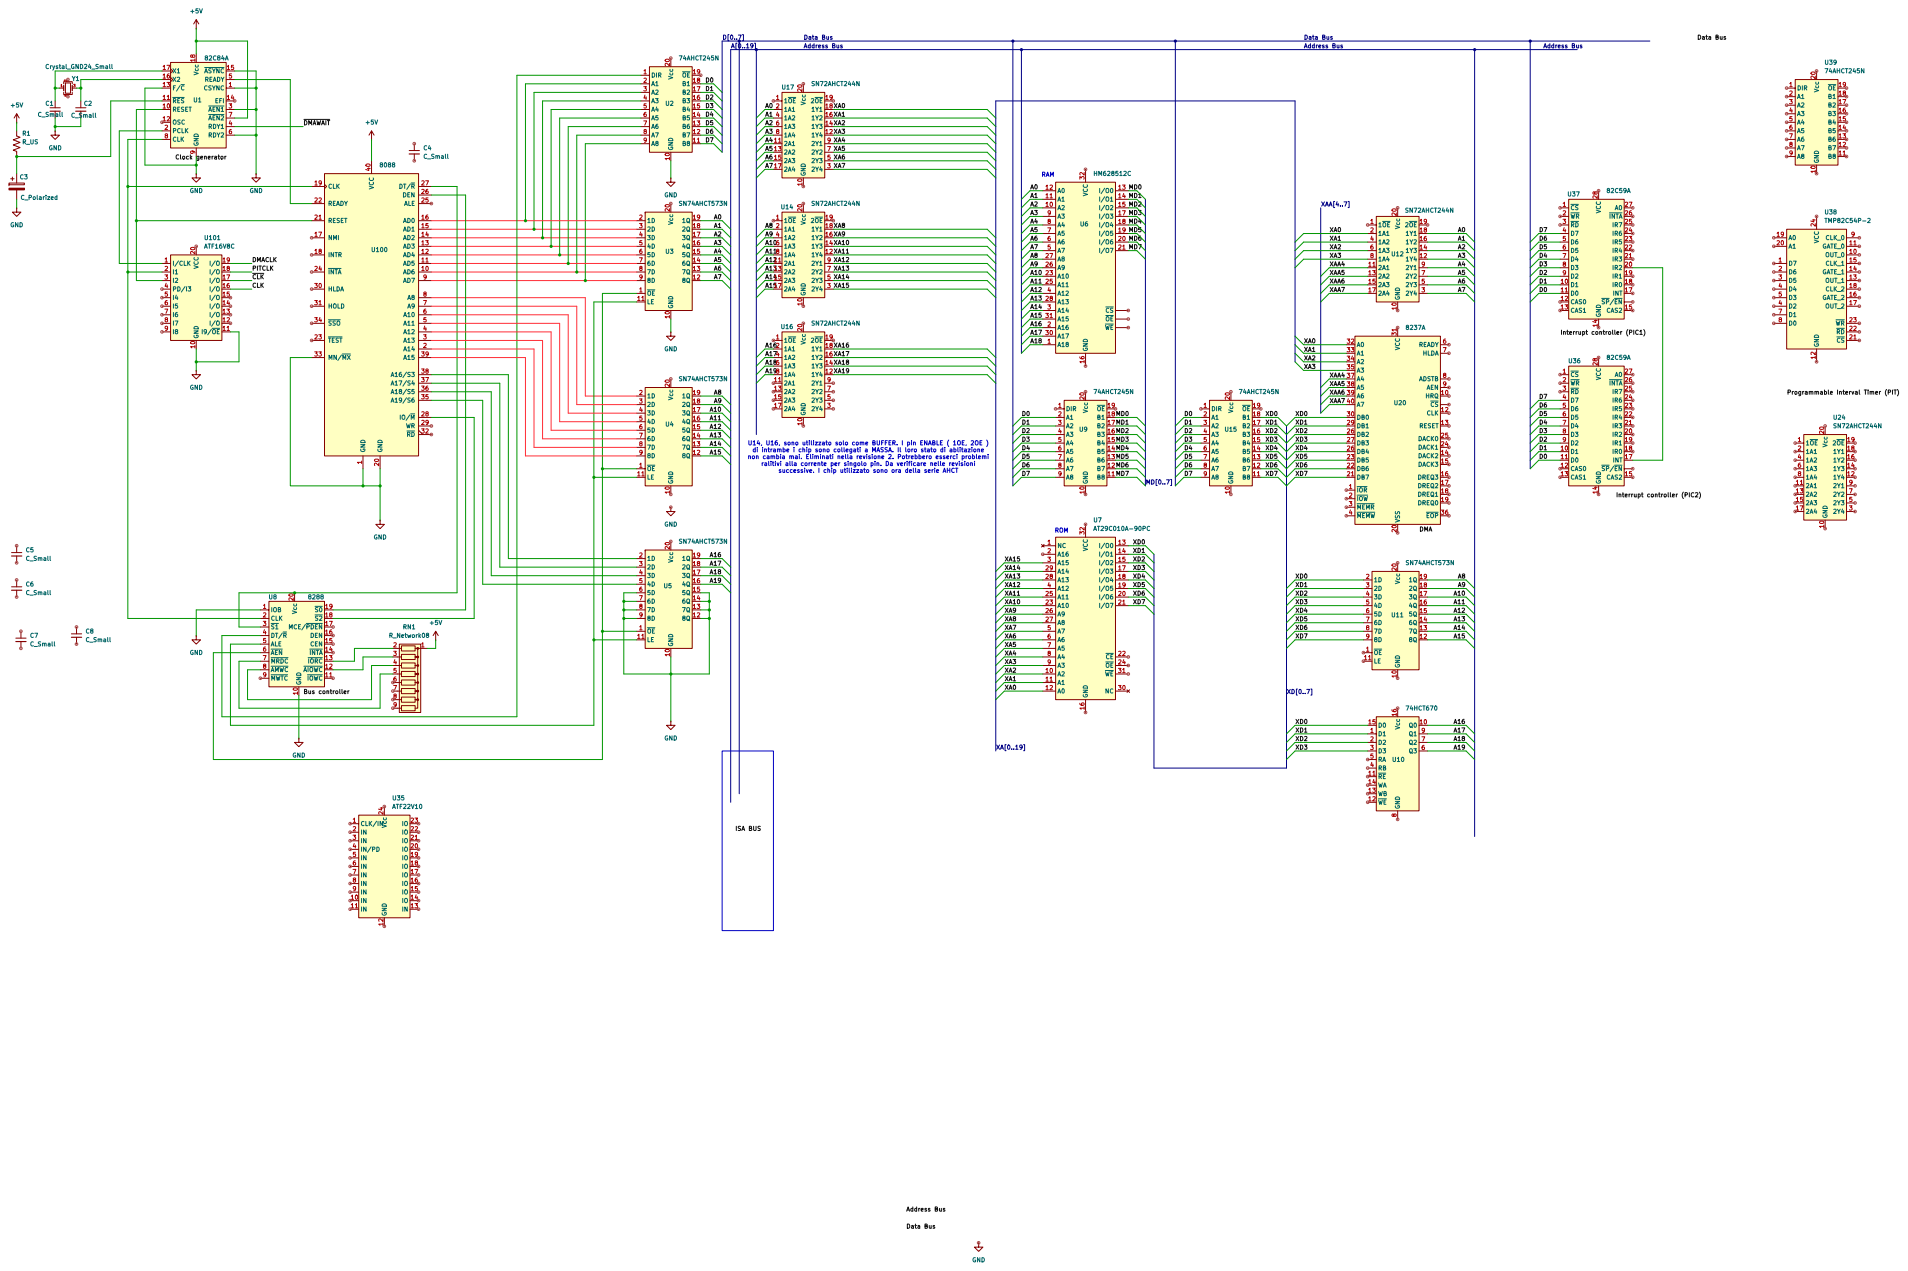
[picture p51: page 1]
