LucaEstiva/Hobby_8088_PC/Schemi/Revisioni/6/Logica_GLUE_Logic.pdf

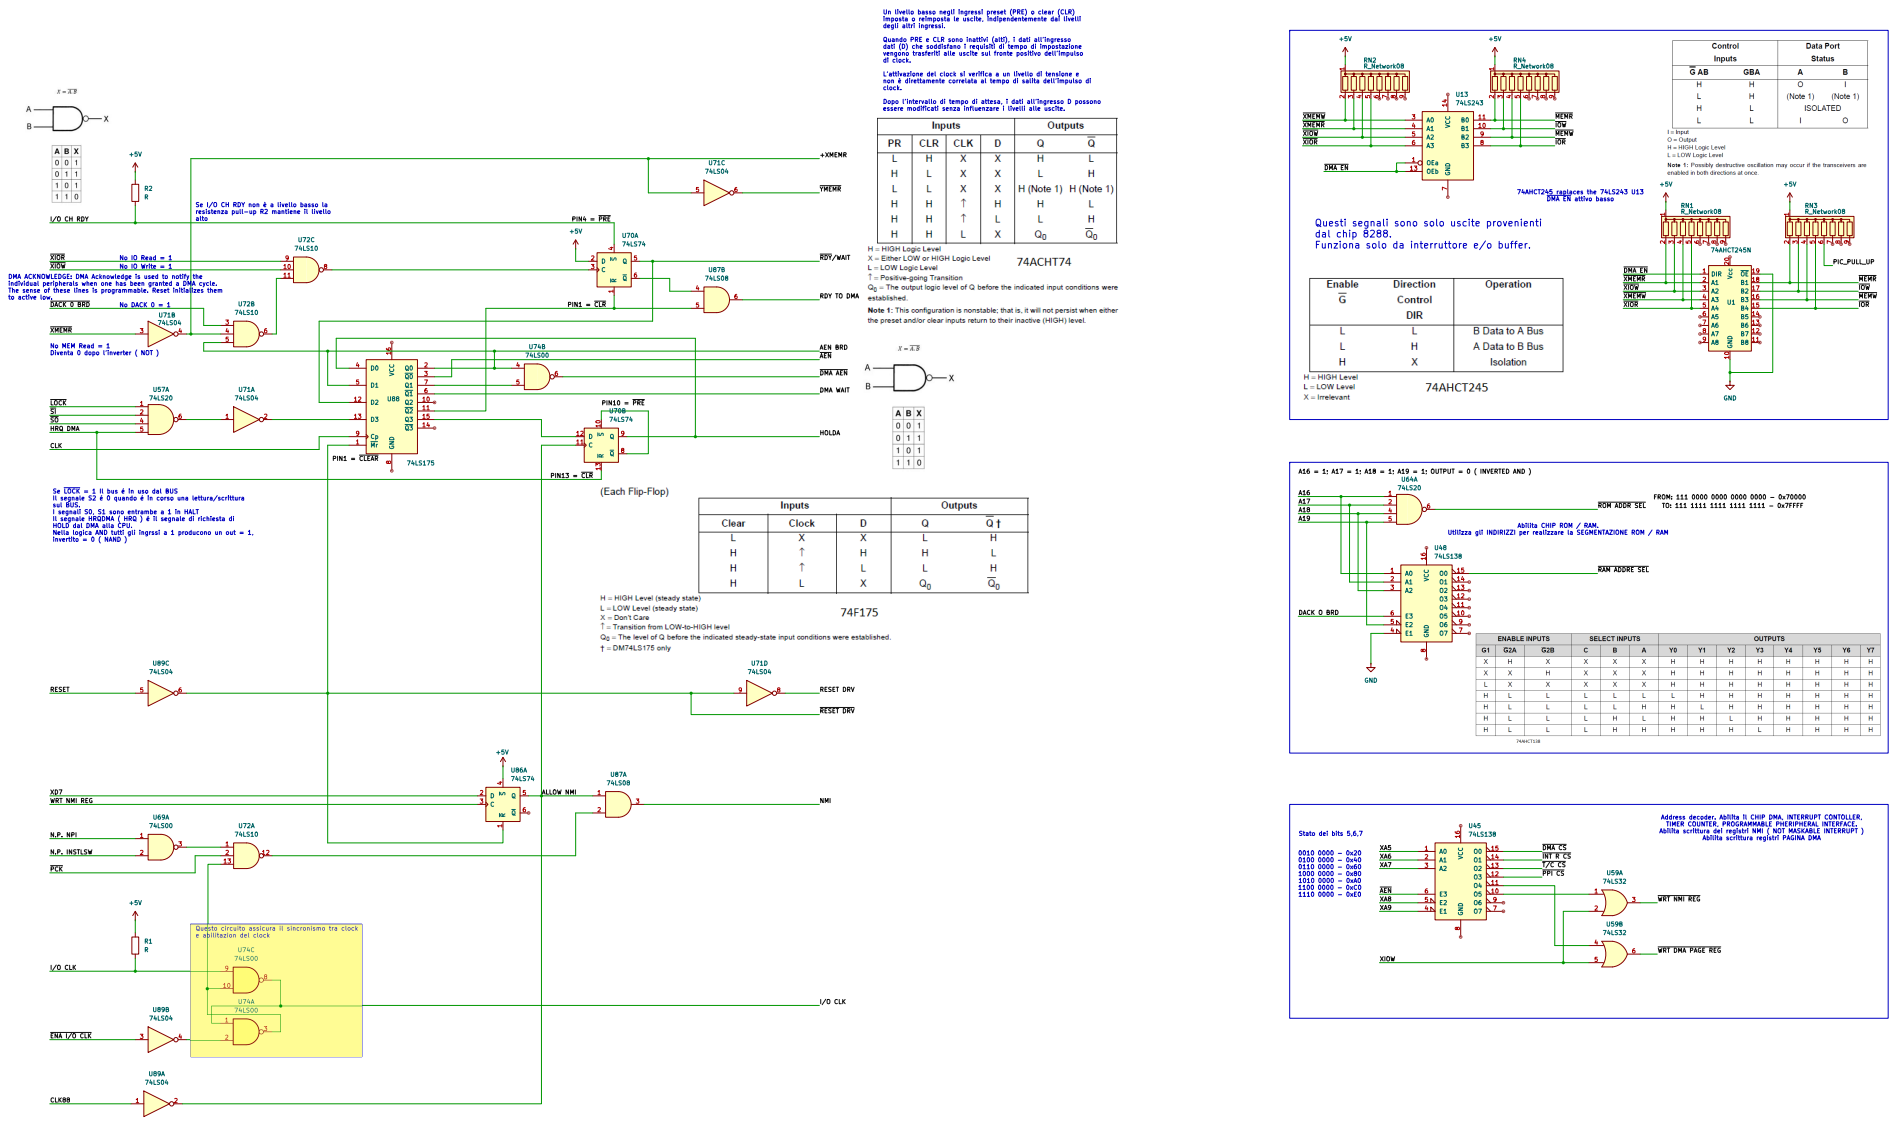
[picture p52: page 1]
