LucaEstiva/Hobby_8088_PC/Schemi/Revisioni/6/Principale.pdf

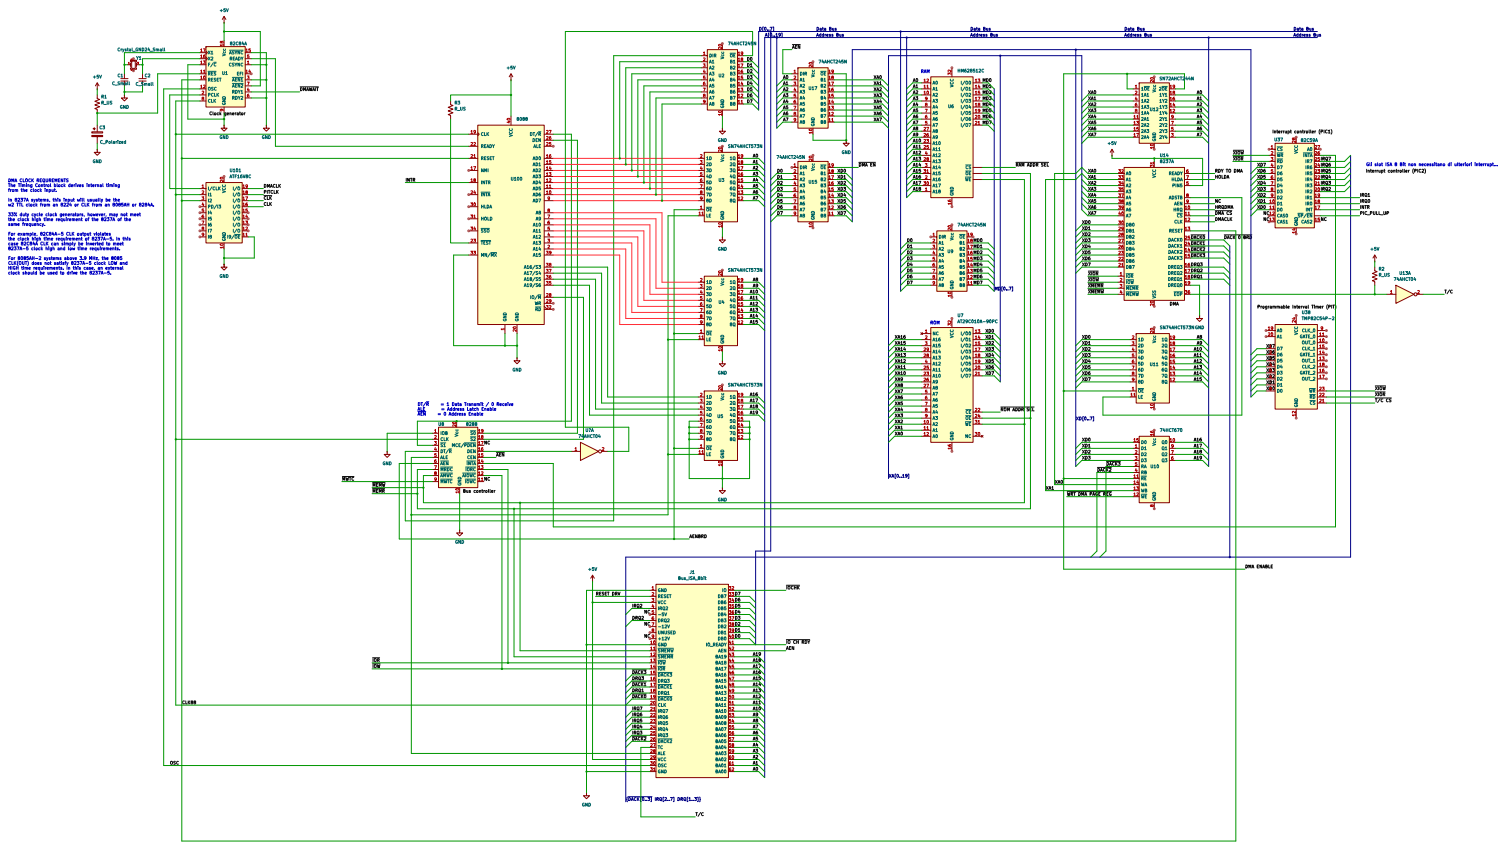
[picture p53: page 1]
