LucaEstiva/Hobby_8088_PC/Schemi/Revisioni/5/Logica_GLUE_Logic.pdf

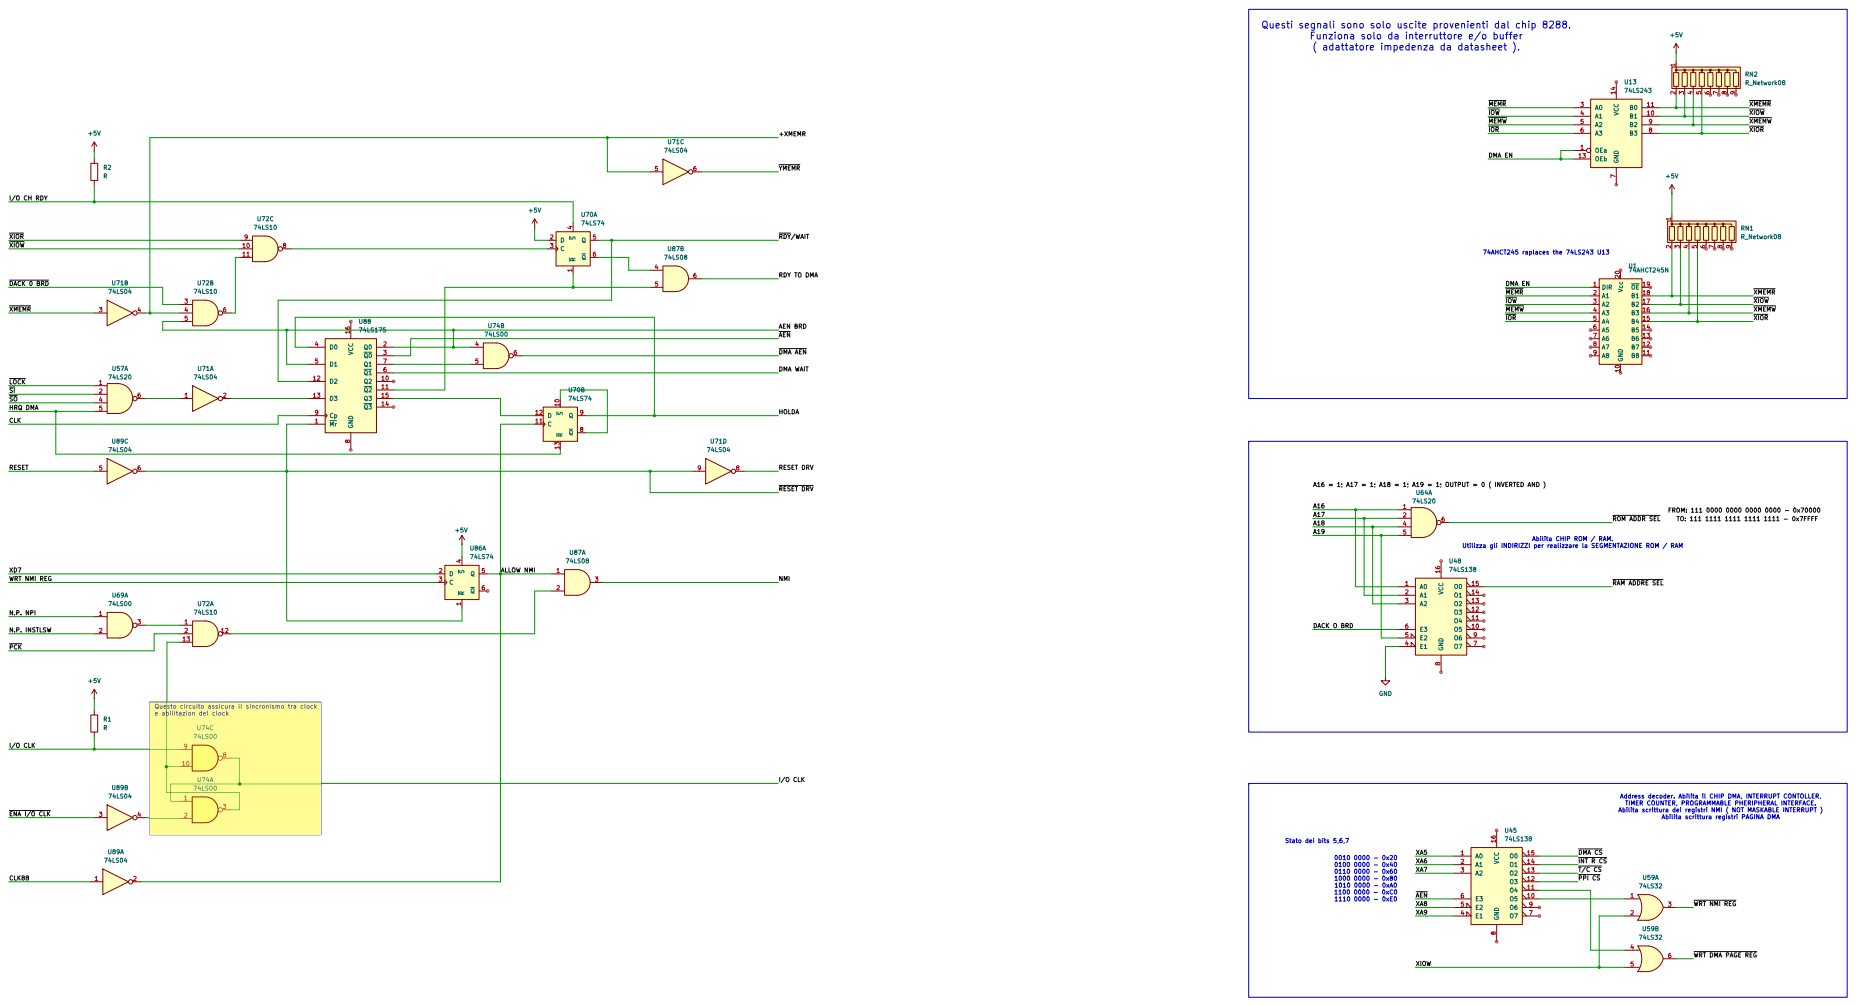
[picture p54: page 1]
