LucaEstiva/Hobby_8088_PC/Schemi/Revisioni/5/Principale.pdf

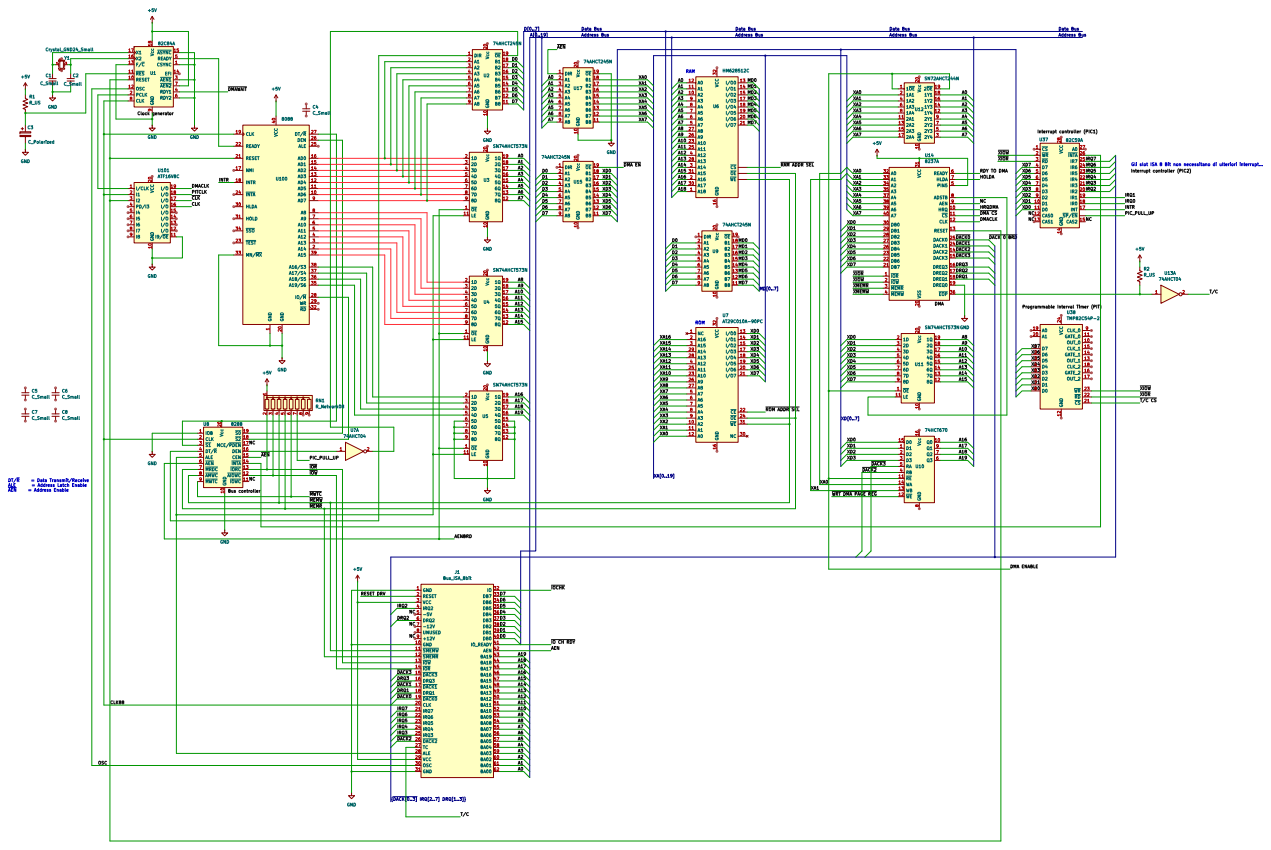
[picture p55: page 1]
