LucaEstiva/Hobby_8088_PC/Schemi/Revisioni/4/Logica_GLUE_Logic.pdf

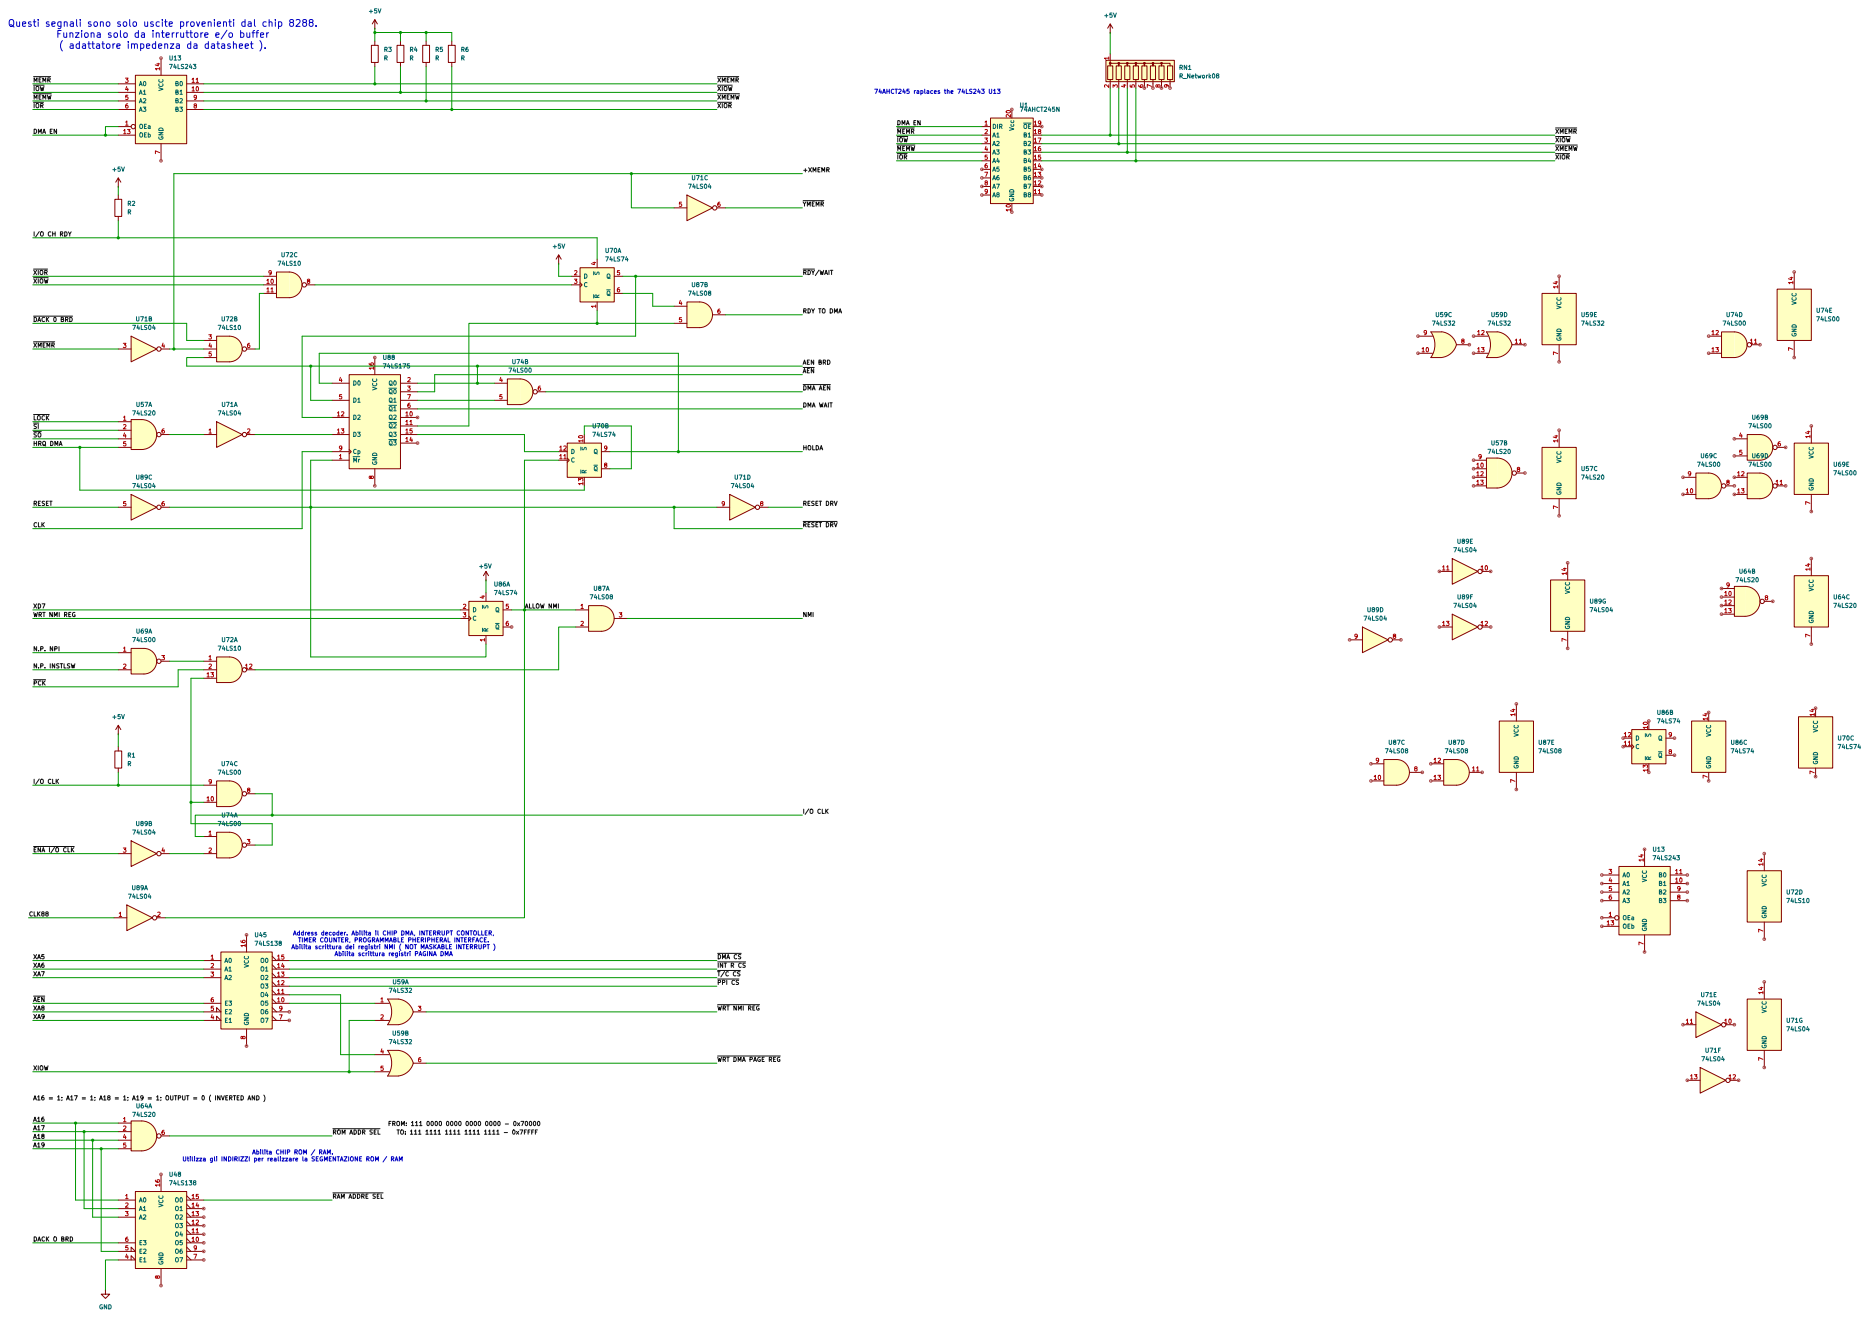
[picture p56: page 1]
