LucaEstiva/Hobby_8088_PC/Schemi/Revisioni/4/Principale.pdf

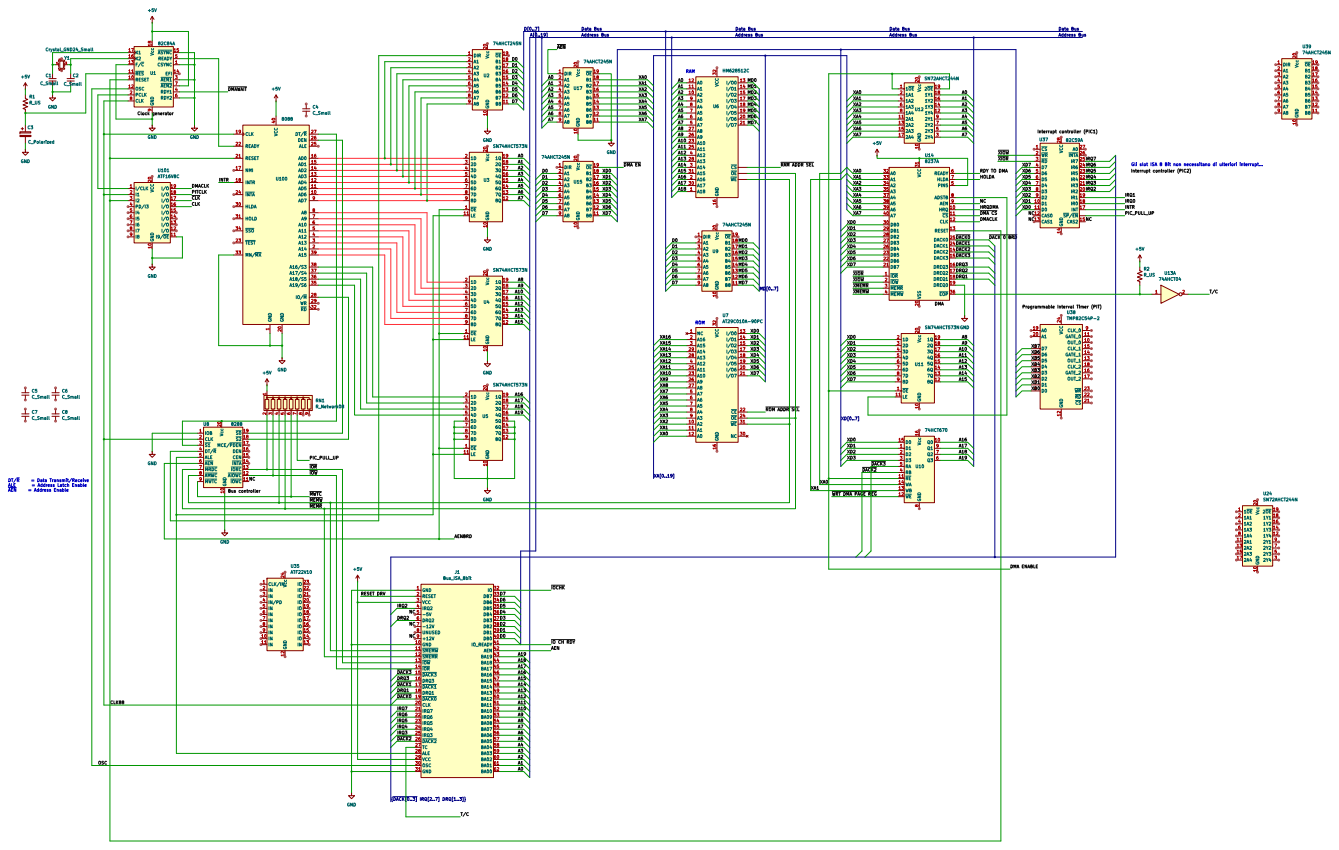
[picture p57: page 1]
