LucaEstiva/Hobby_8088_PC/Schemi/Revisioni/3/Logica_GLUE_Logic.pdf

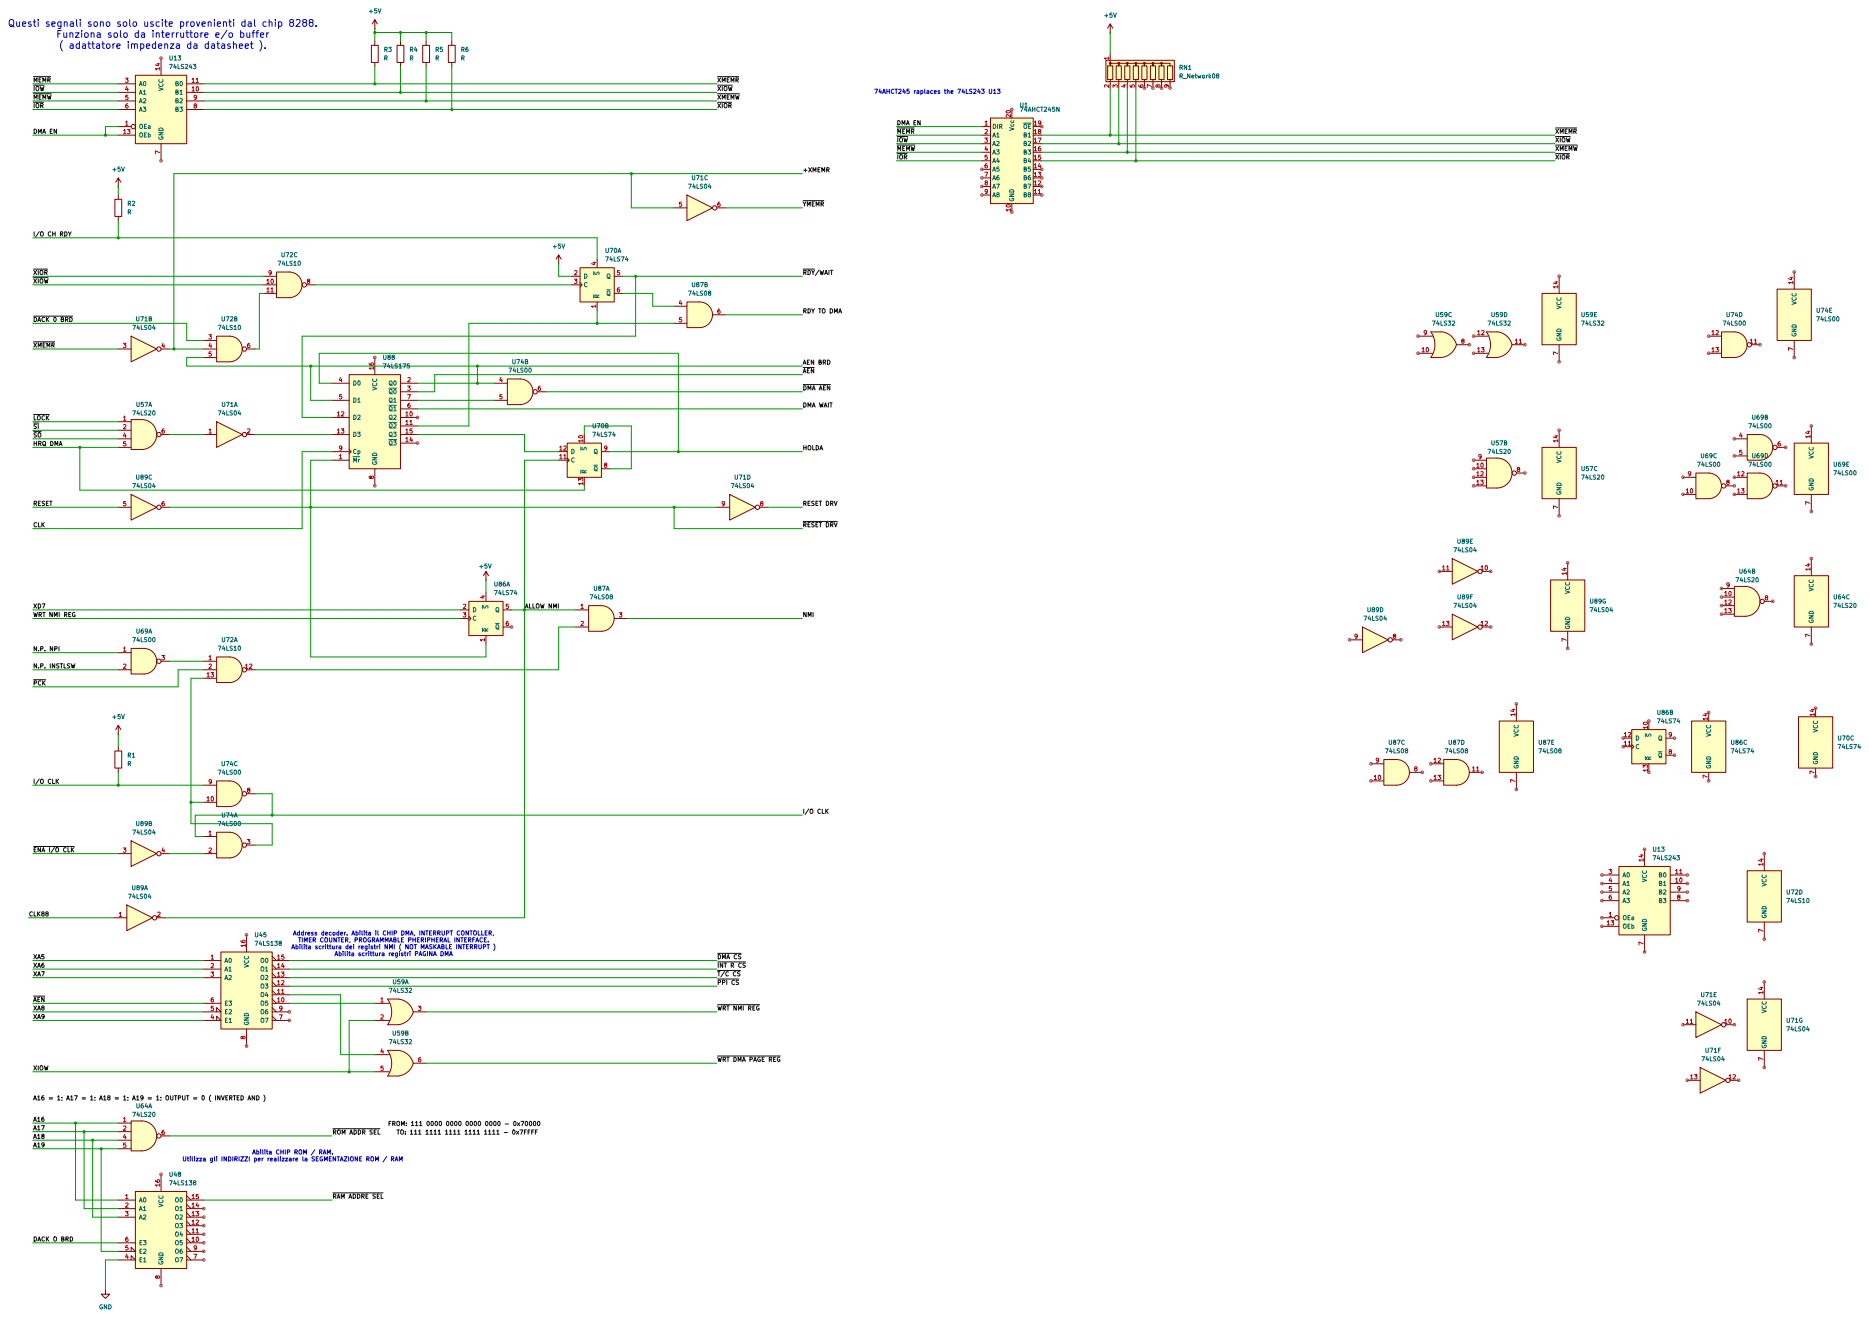
[picture p58: page 1]
