LucaEstiva/Hobby_8088_PC/Schemi/Revisioni/3/Principale.pdf

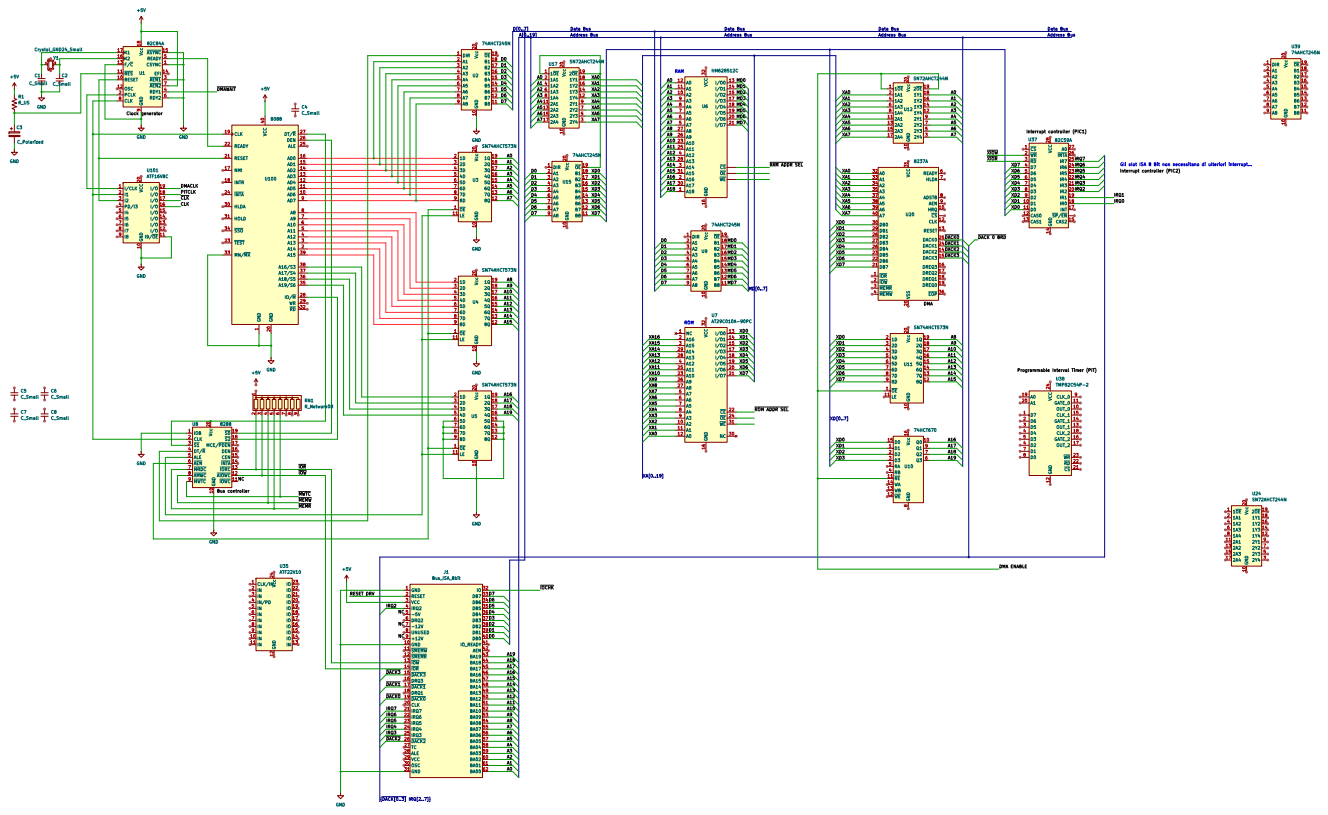
[picture p59: page 1]
