LucaEstiva/Hobby_8088_PC/Schemi/Revisioni/2/Logica_GLUE_Logic.pdf

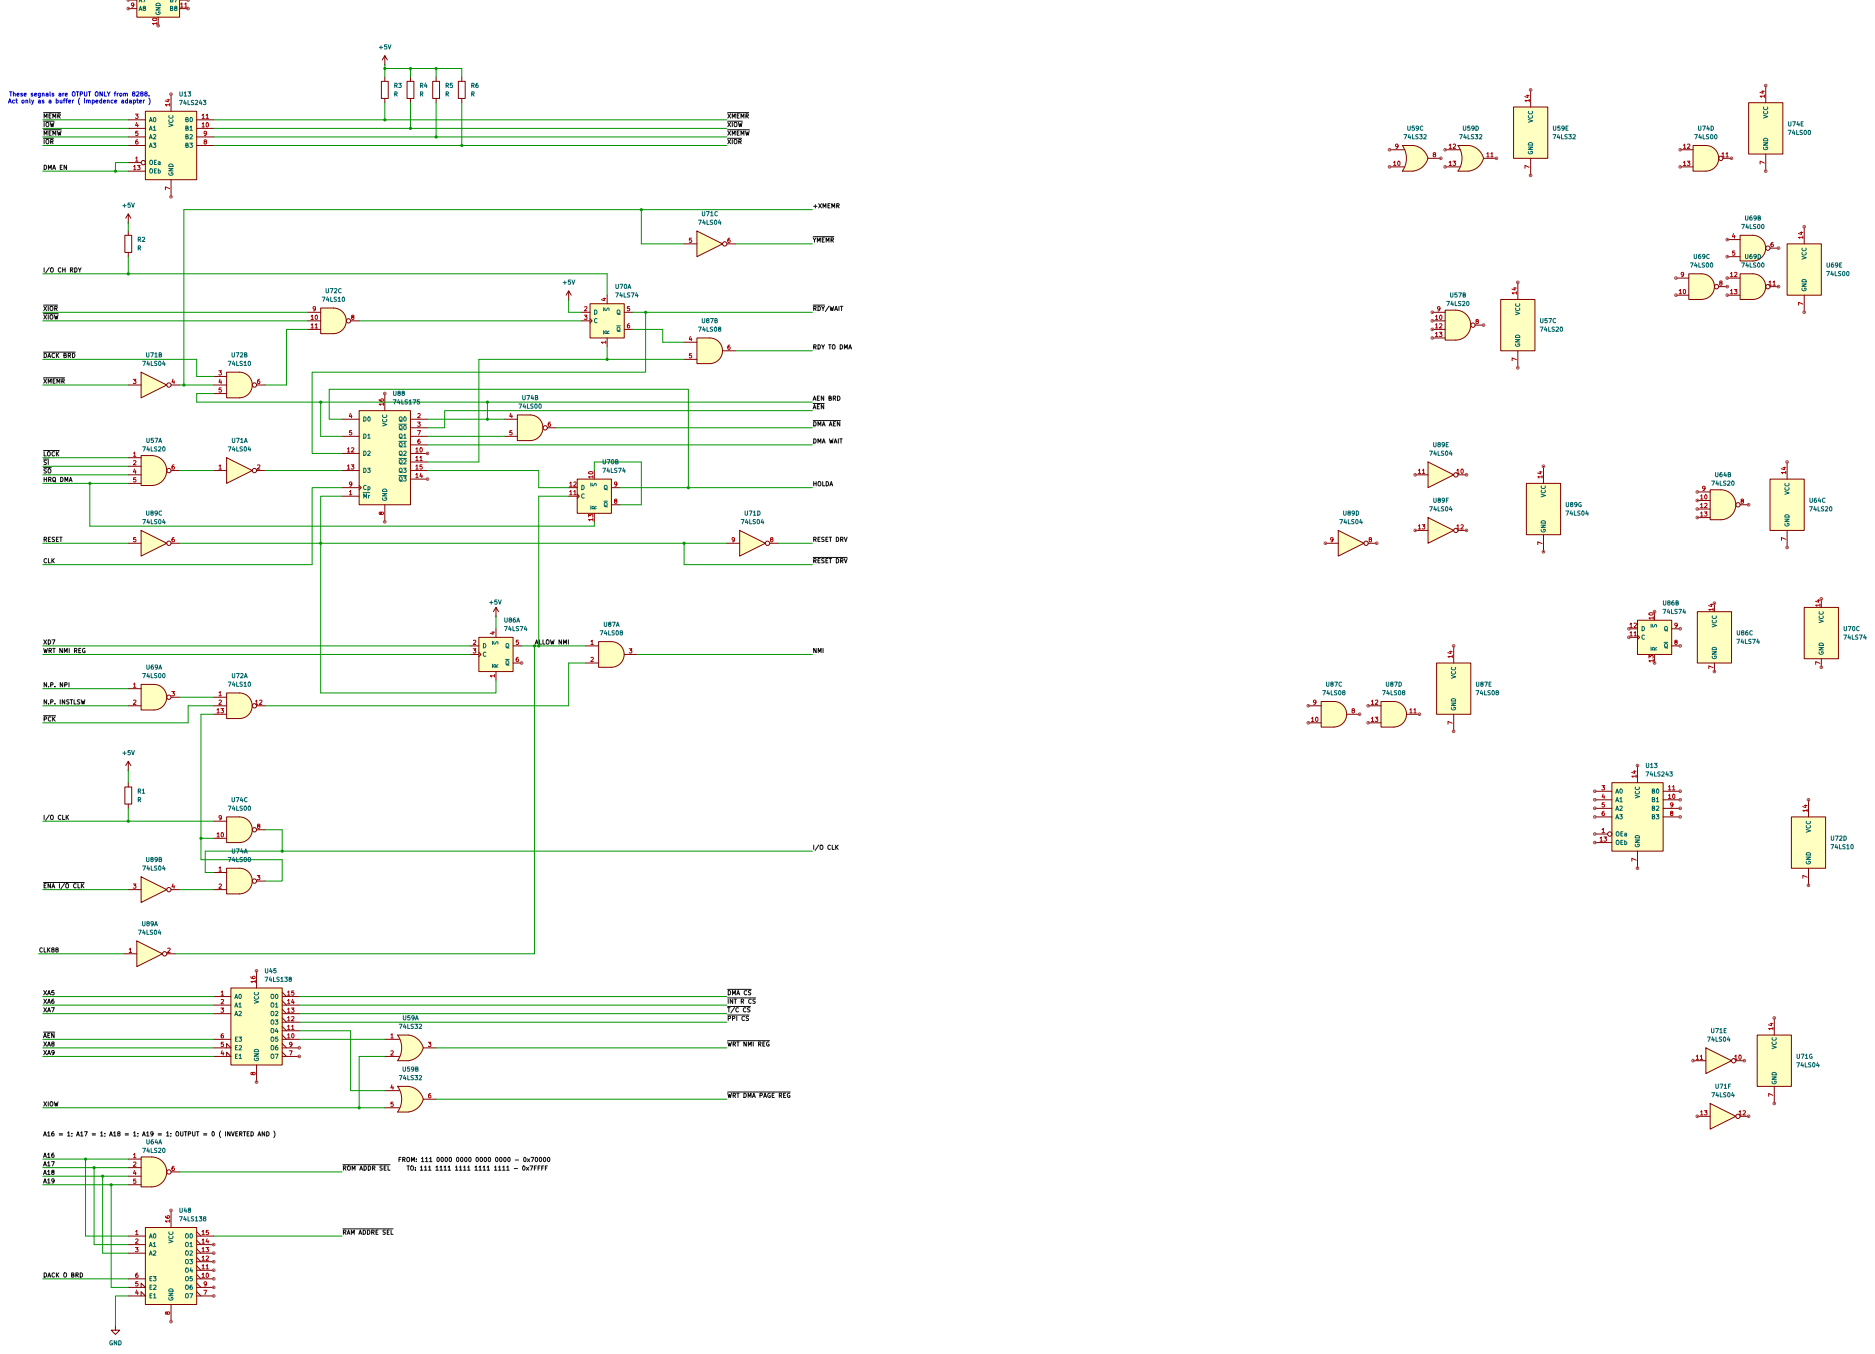
[picture p60: page 1]
