LucaEstiva/Hobby_8088_PC/Schemi/Revisioni/2/Principale.pdf

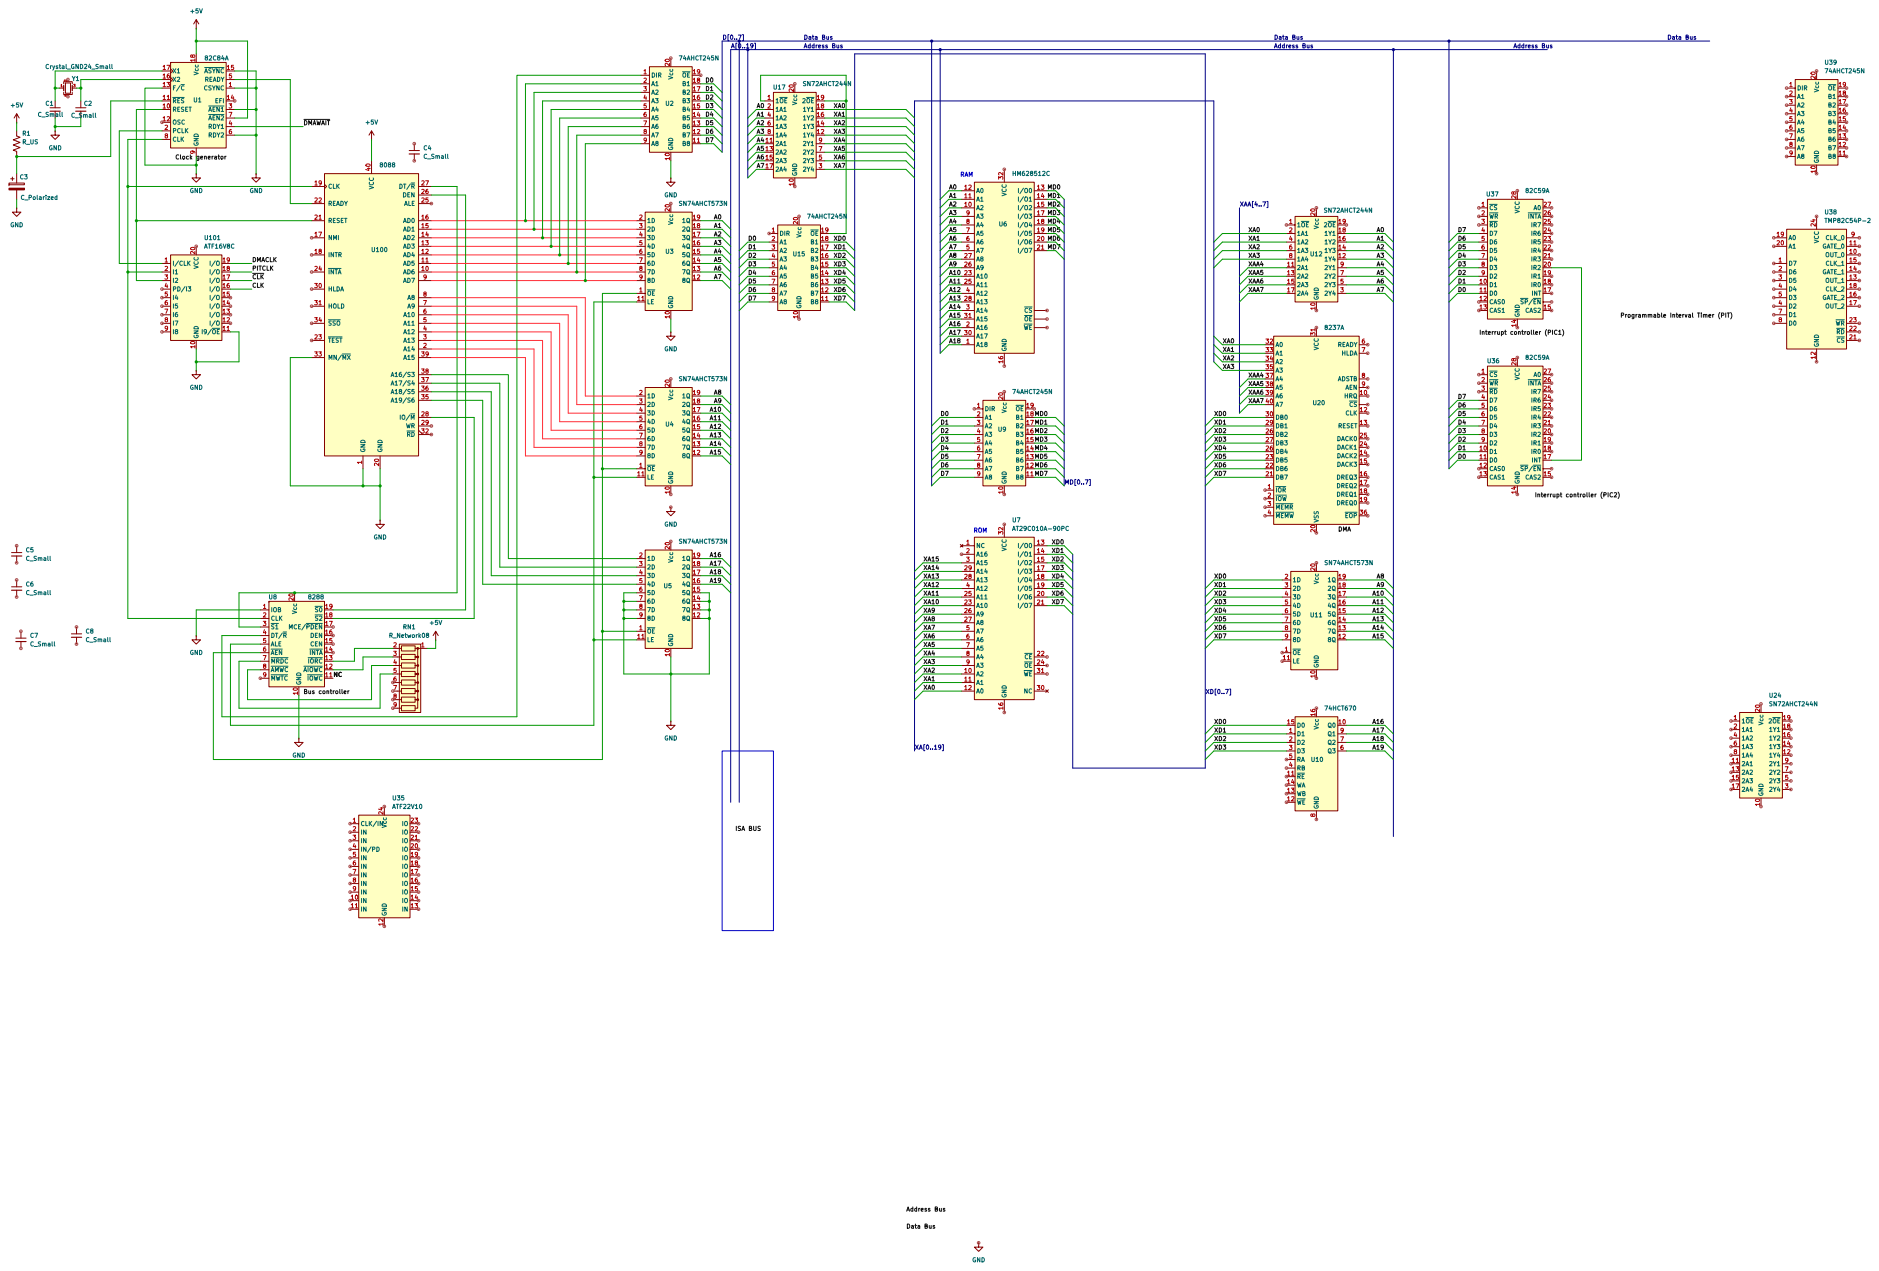
[picture p61: page 1]
