LucaEstiva/Hobby_8088_PC/Schemi/Revisioni/1/Logica_GLUE_Logic.pdf

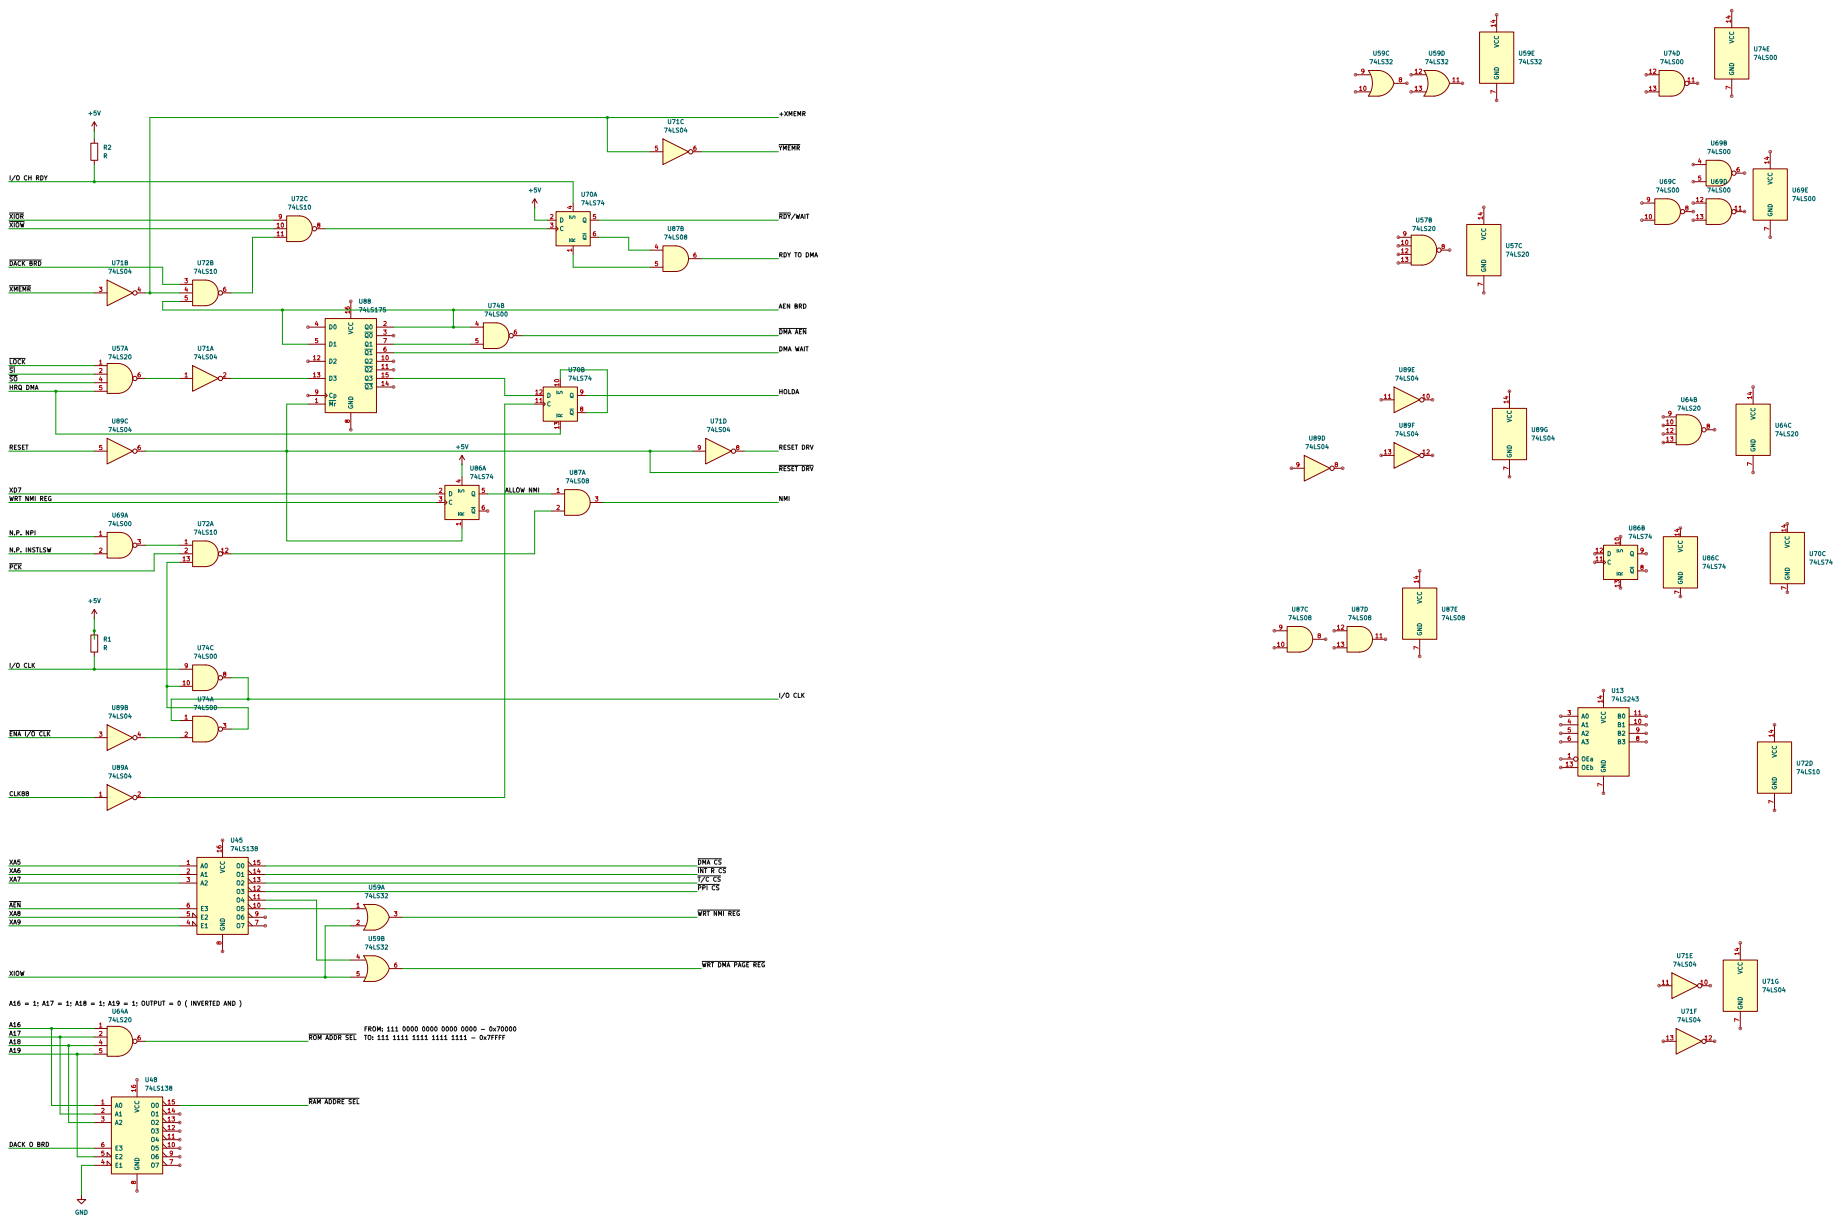
[picture p62: page 1]
