LucaEstiva/Hobby_8088_PC/Schemi/Revisioni/1/Principale.pdf

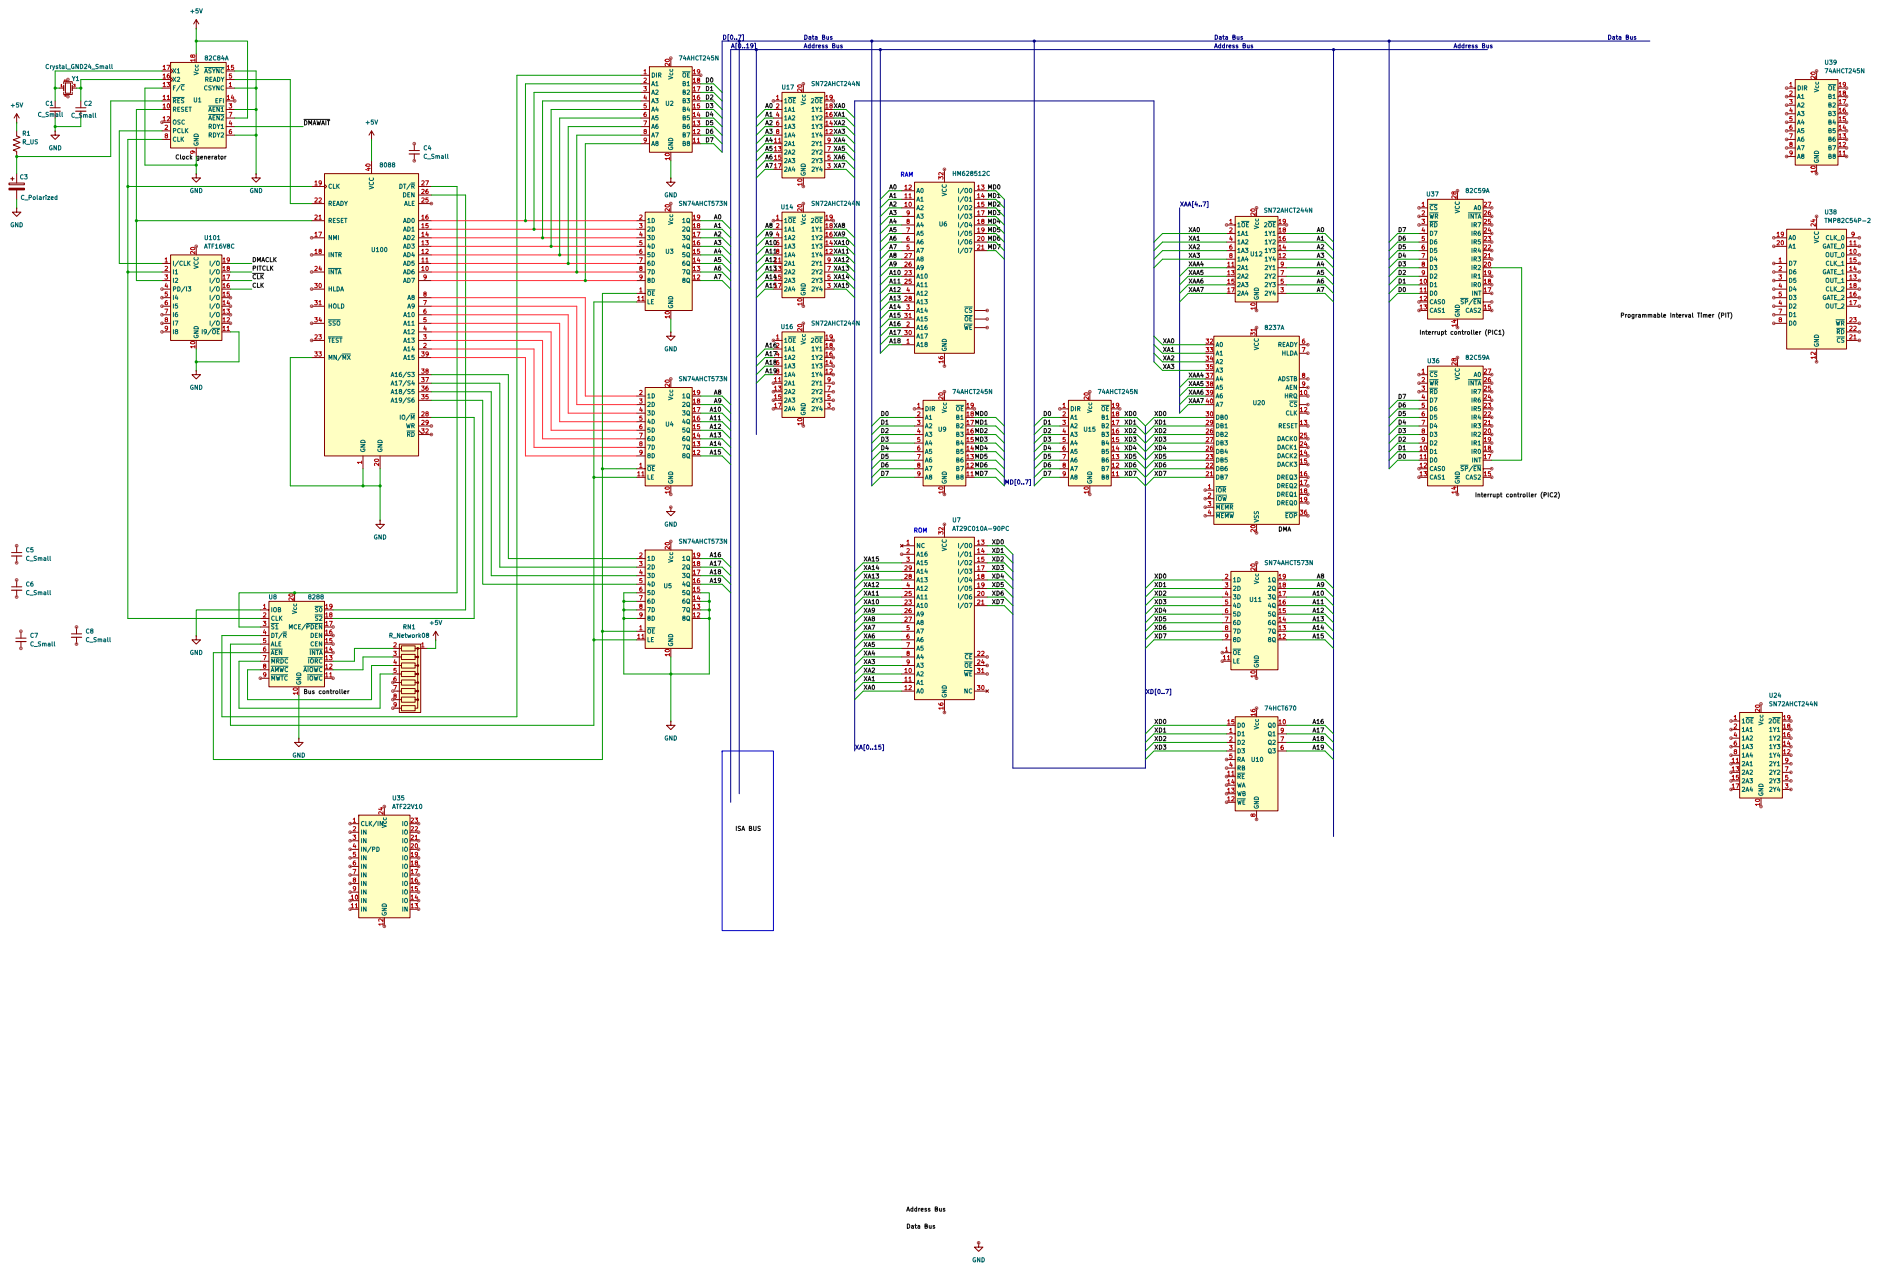
[picture p63: page 1]
